earlynerd/ELRS-haptics/hardware/archive/combined-project/README.md

# Archived combined project

This superseded eight-island project was moved here intact on 2026-09-13. It includes the user's top-sheet redraw and the last combined PCB. It is retained for provenance, not active editing.

Open `../../main/main.kicad_pro` and `../../satellite/satellite.kicad_pro` for current work. The end-only R53 bridge is replaced by JP1 on the universal satellite.

Original hashes and an independent snapshot are under `../../backups/before-two-projects/`. No components were missing from the redraw; its two split power aliases are repaired in the new projects.
