earlynerd/ELRS-haptics/hardware/preview/lra-contact.png

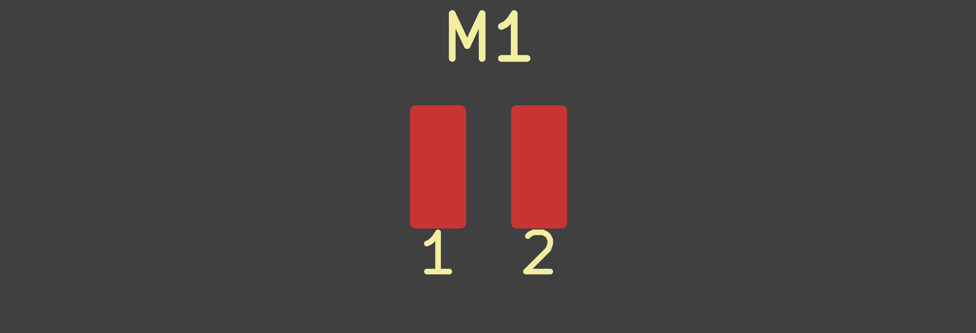
hardware/preview/lra-contact.png
