earlynerd/ELRS-haptics/hardware/preview/pack-protection/power.png

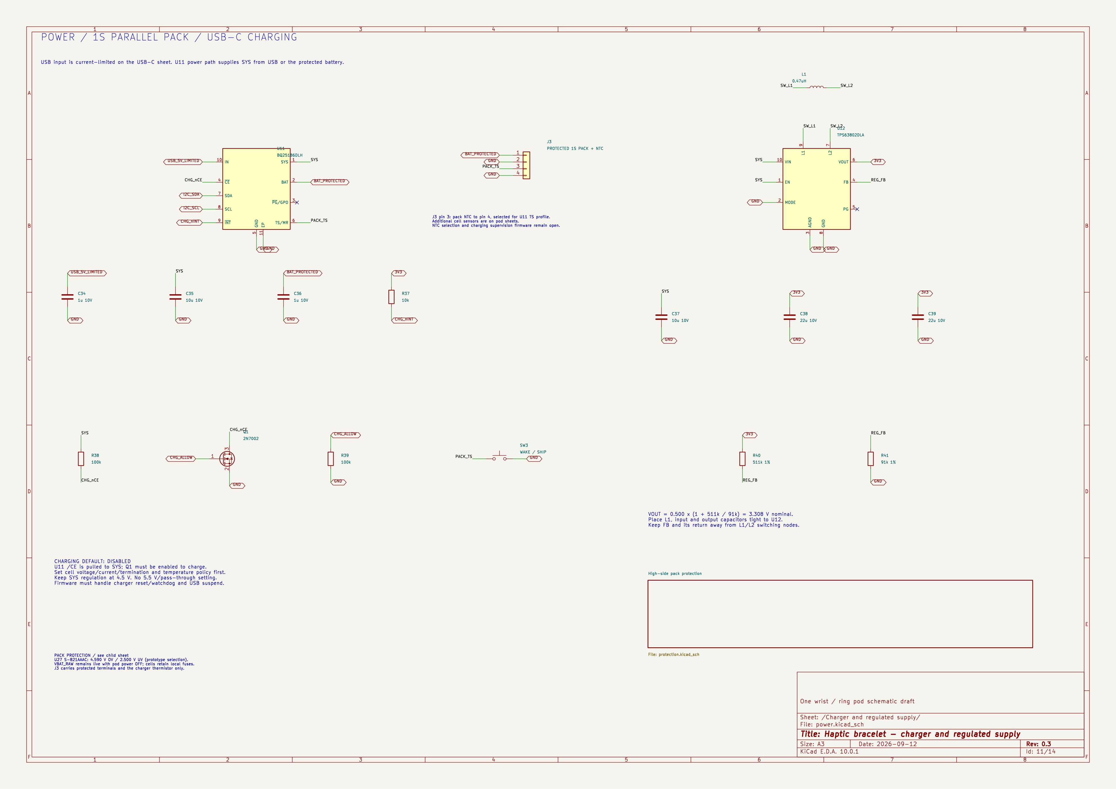
hardware/preview/pack-protection/power.png
