earlynerd/ELRS-haptics/hardware/preview/pack-protection/protection.png

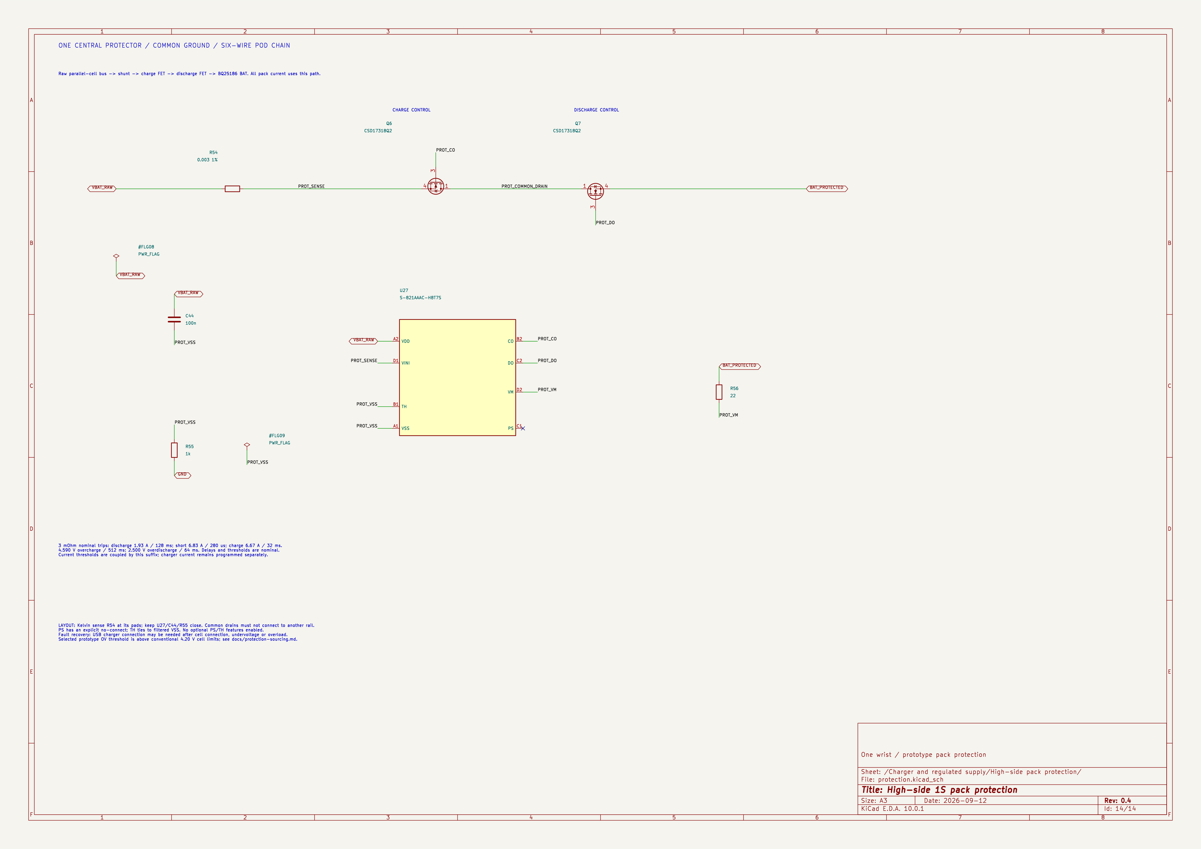
hardware/preview/pack-protection/protection.png
