earlynerd/ELRS-haptics/hardware/preview/placement.png

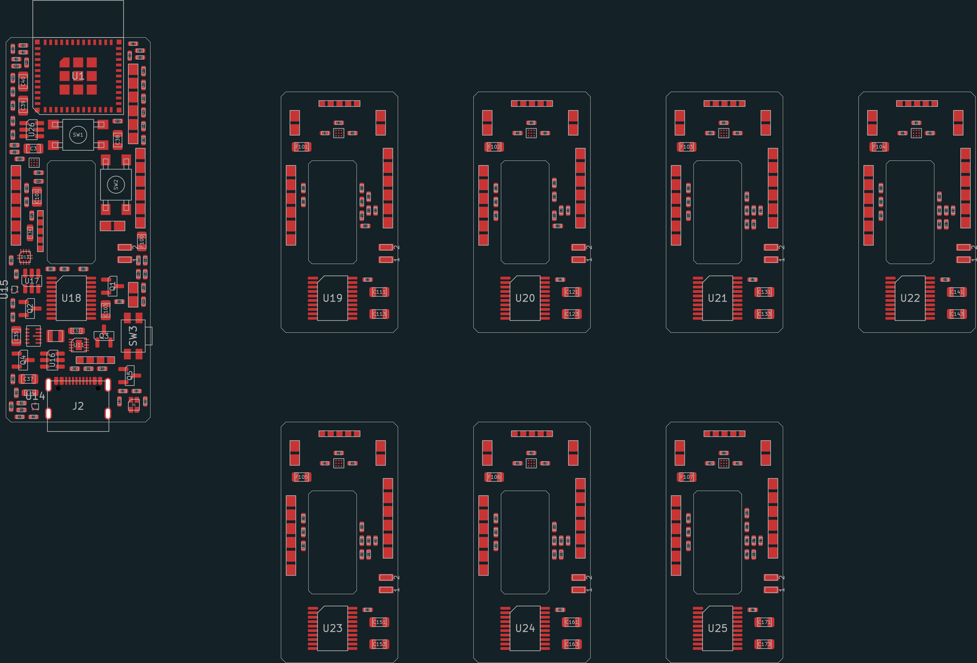
hardware/preview/placement.png
