earlynerd/ELRS-haptics/hardware/preview/protected-cells/haptic-bracelet-Eight ring pods-Pod 0 _ U18.png

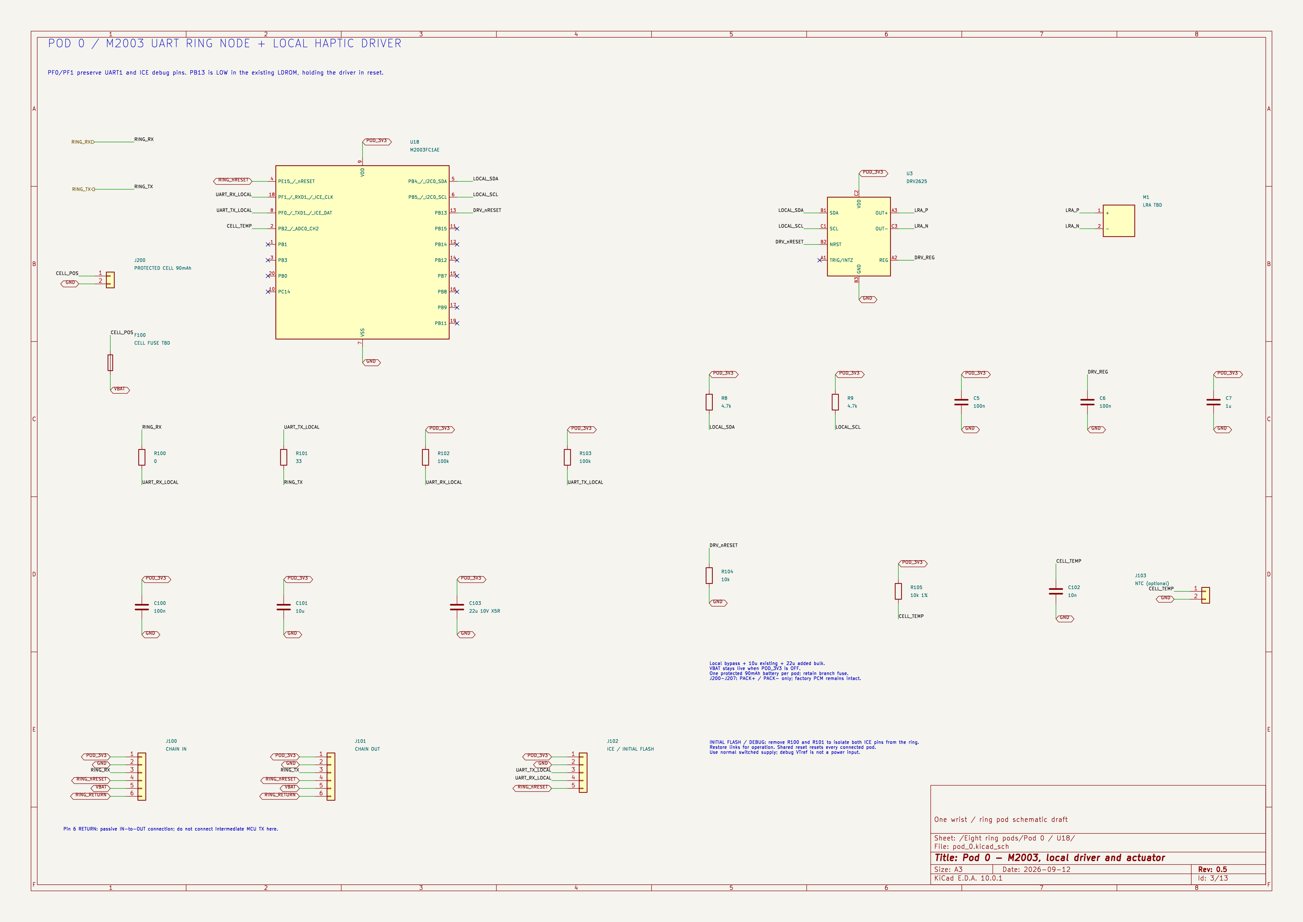
hardware/preview/protected-cells/haptic-bracelet-Eight ring pods-Pod 0 _ U18.png
