earlynerd/ELRS-haptics/hardware/preview/protected-cells/haptic-bracelet-Eight ring pods.png

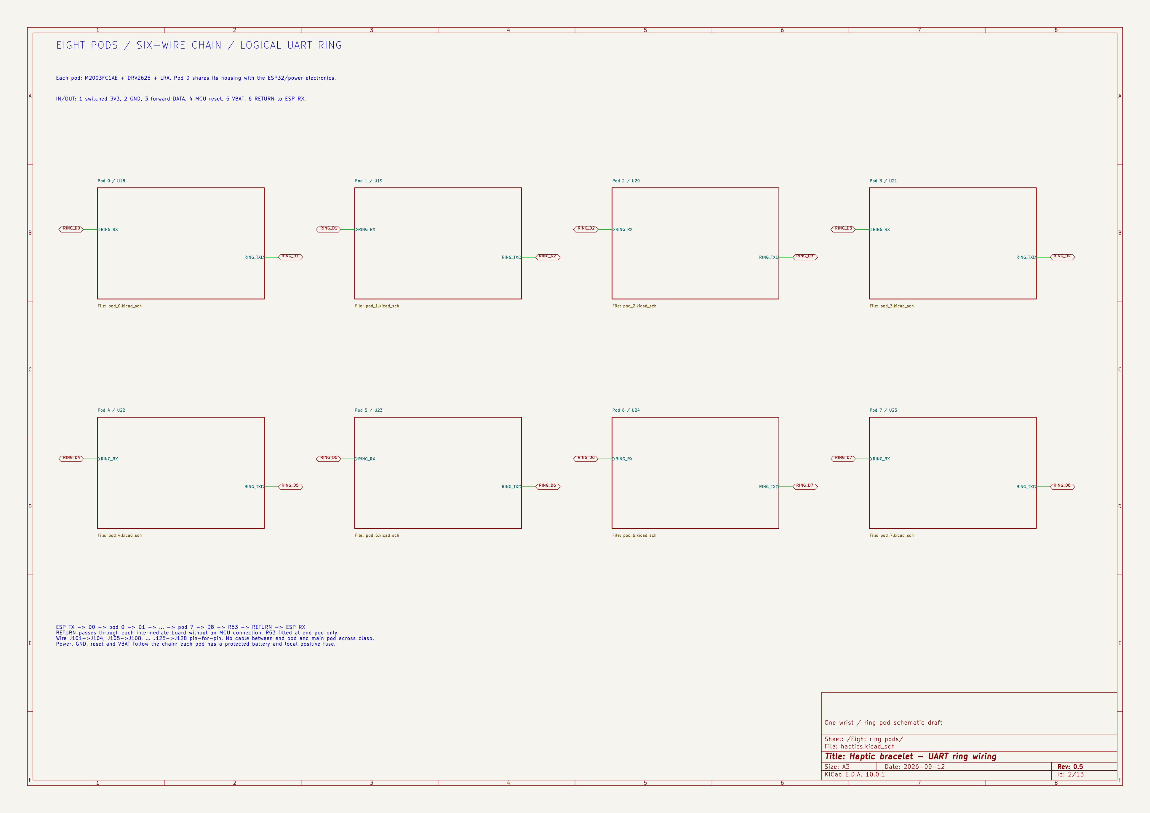
hardware/preview/protected-cells/haptic-bracelet-Eight ring pods.png
