earlynerd/ELRS-haptics/hardware/preview/protected-cells/haptic-bracelet-USB-C data and power.png

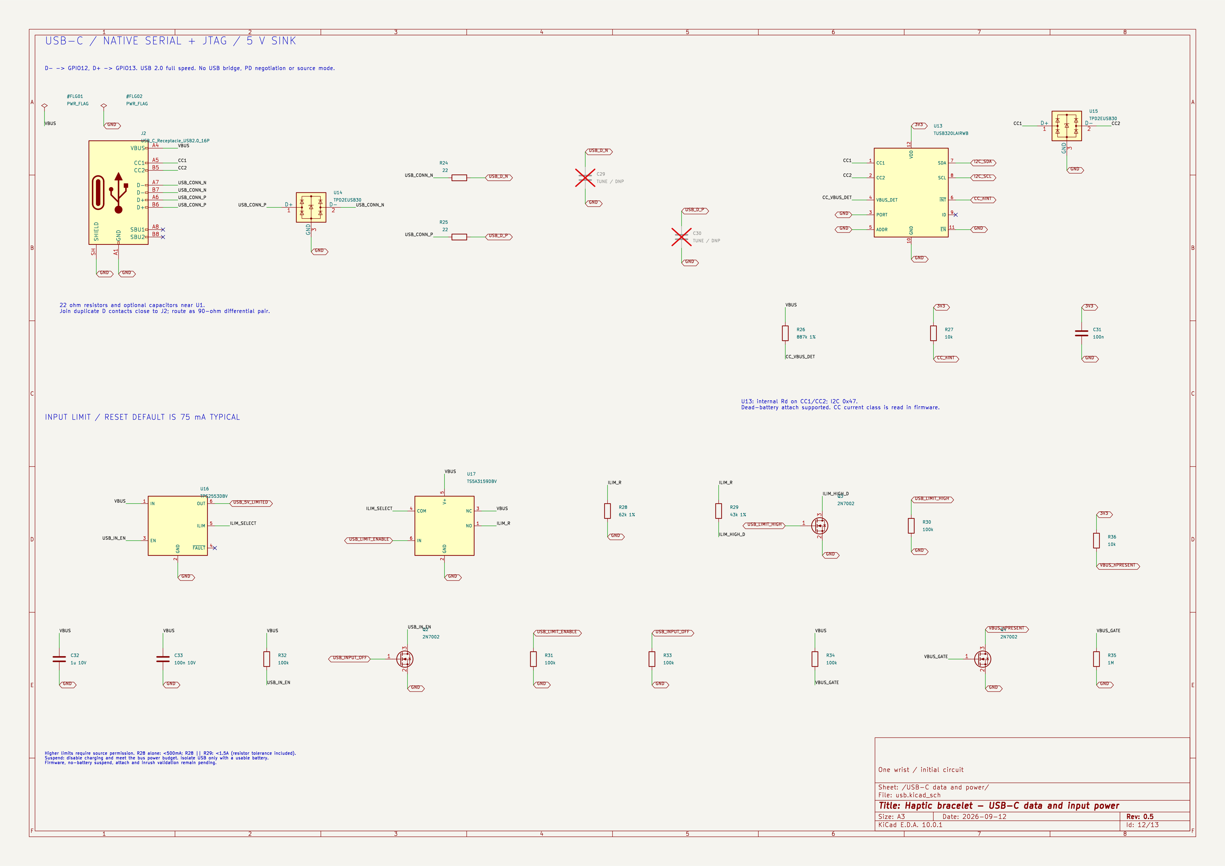
hardware/preview/protected-cells/haptic-bracelet-USB-C data and power.png
