earlynerd/ELRS-haptics/hardware/preview/protected-cells/haptic-bracelet.png

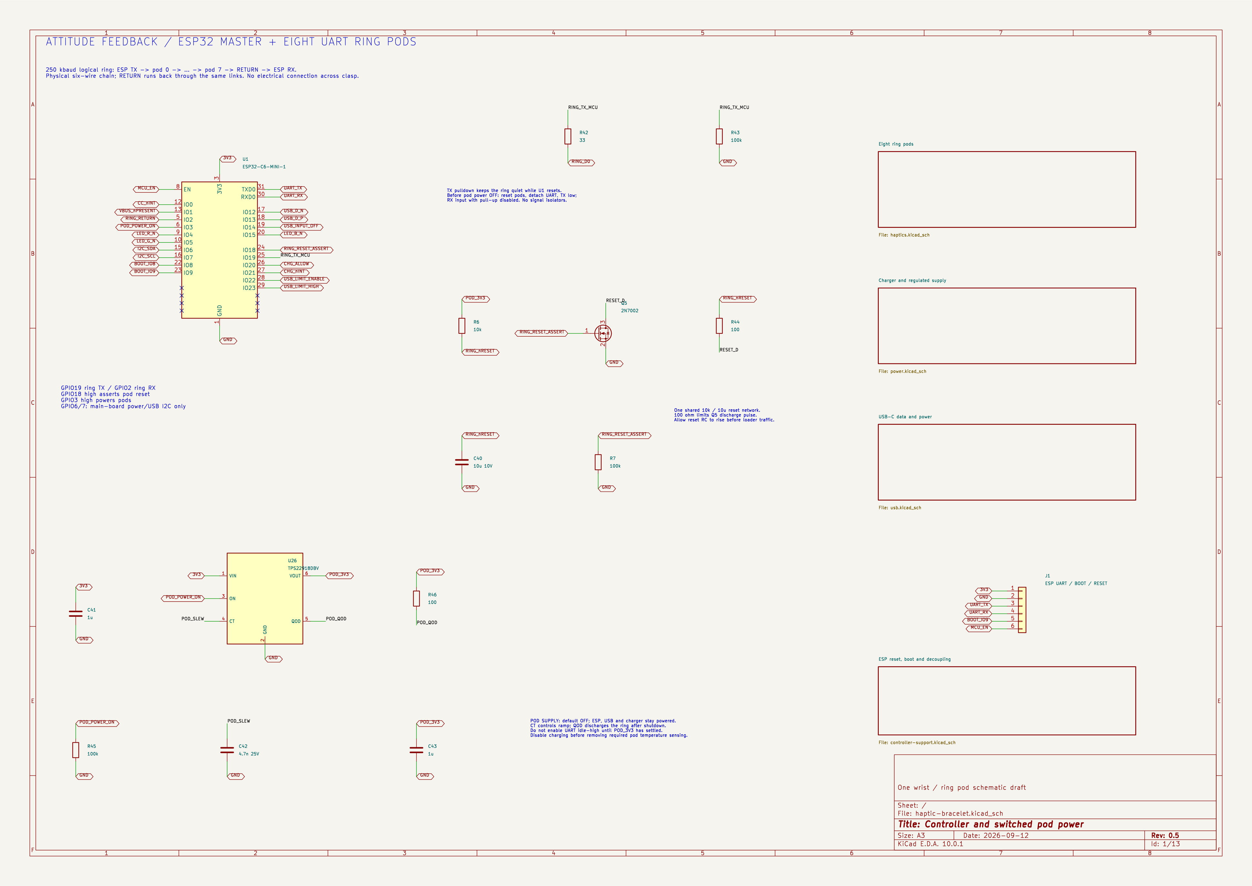
hardware/preview/protected-cells/haptic-bracelet.png
