earlynerd/ELRS-haptics/hardware/preview/ring-revision/haptic-bracelet-ESP reset, boot and decoupling.png

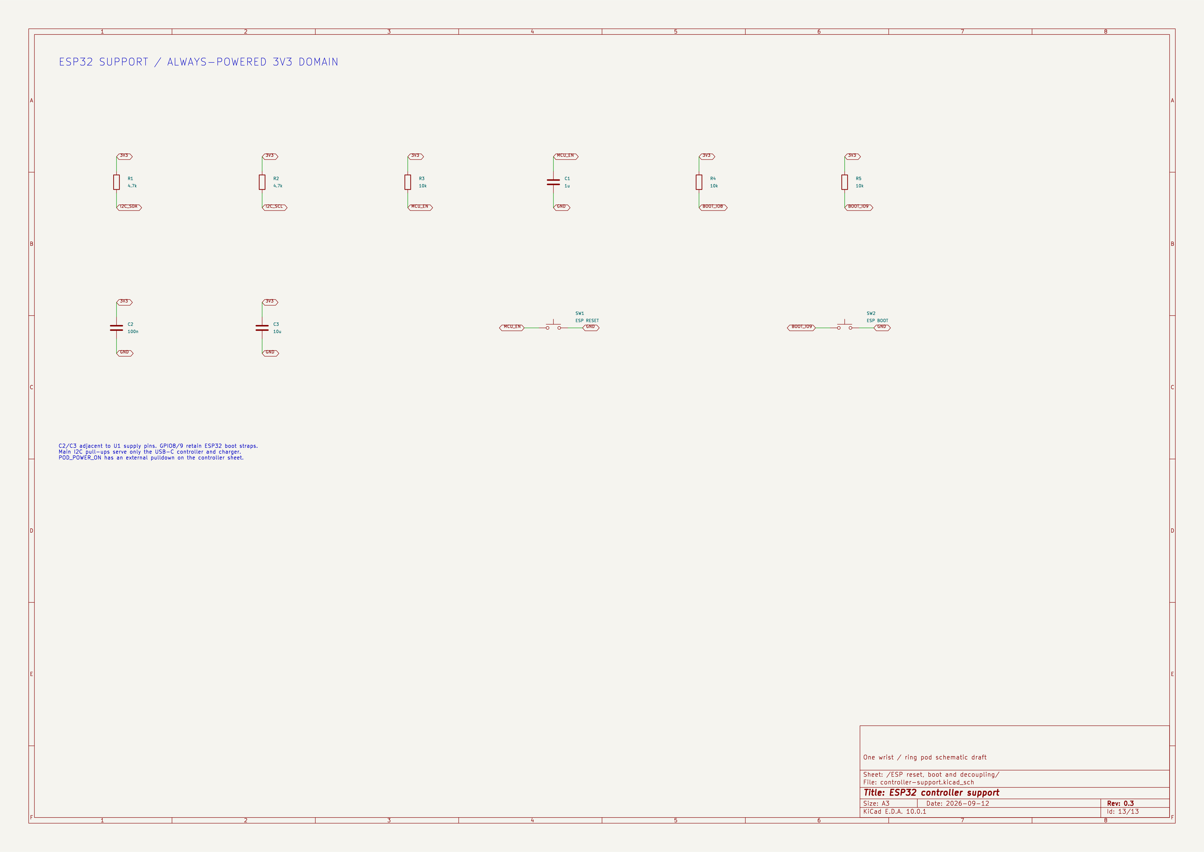
hardware/preview/ring-revision/haptic-bracelet-ESP reset, boot and decoupling.png
