earlynerd/ELRS-haptics/hardware/preview/serial-return/end-pod.png

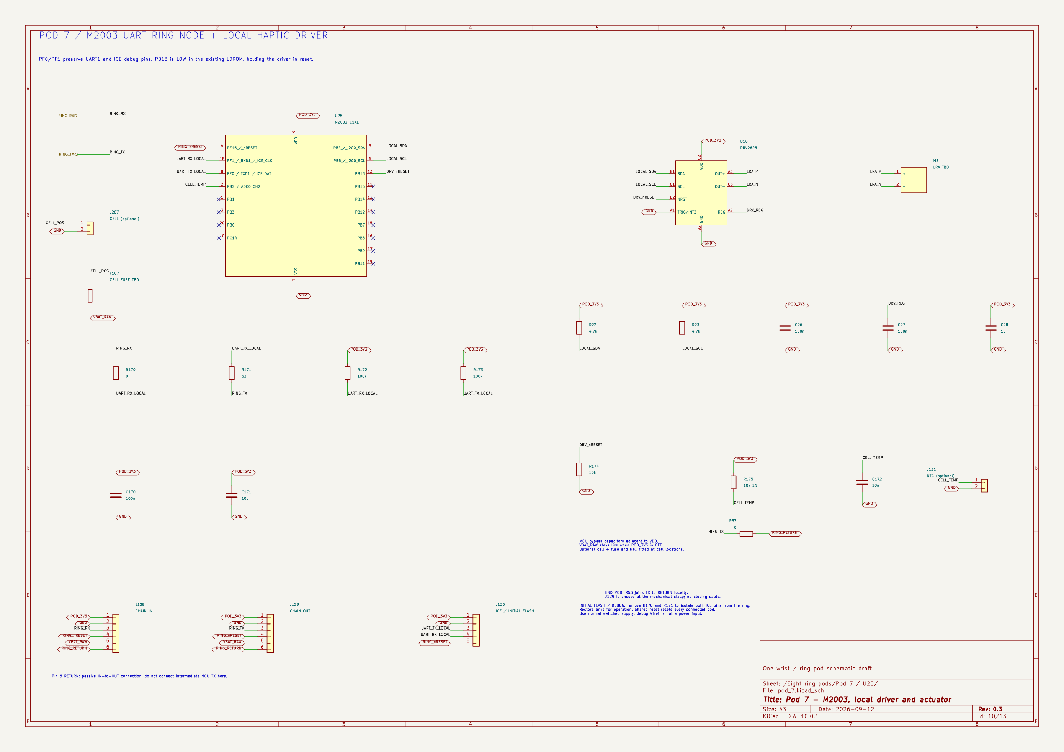
hardware/preview/serial-return/end-pod.png
