earlynerd/ELRS-haptics/hardware/verification/routing-v09/main-placement-proposal.png

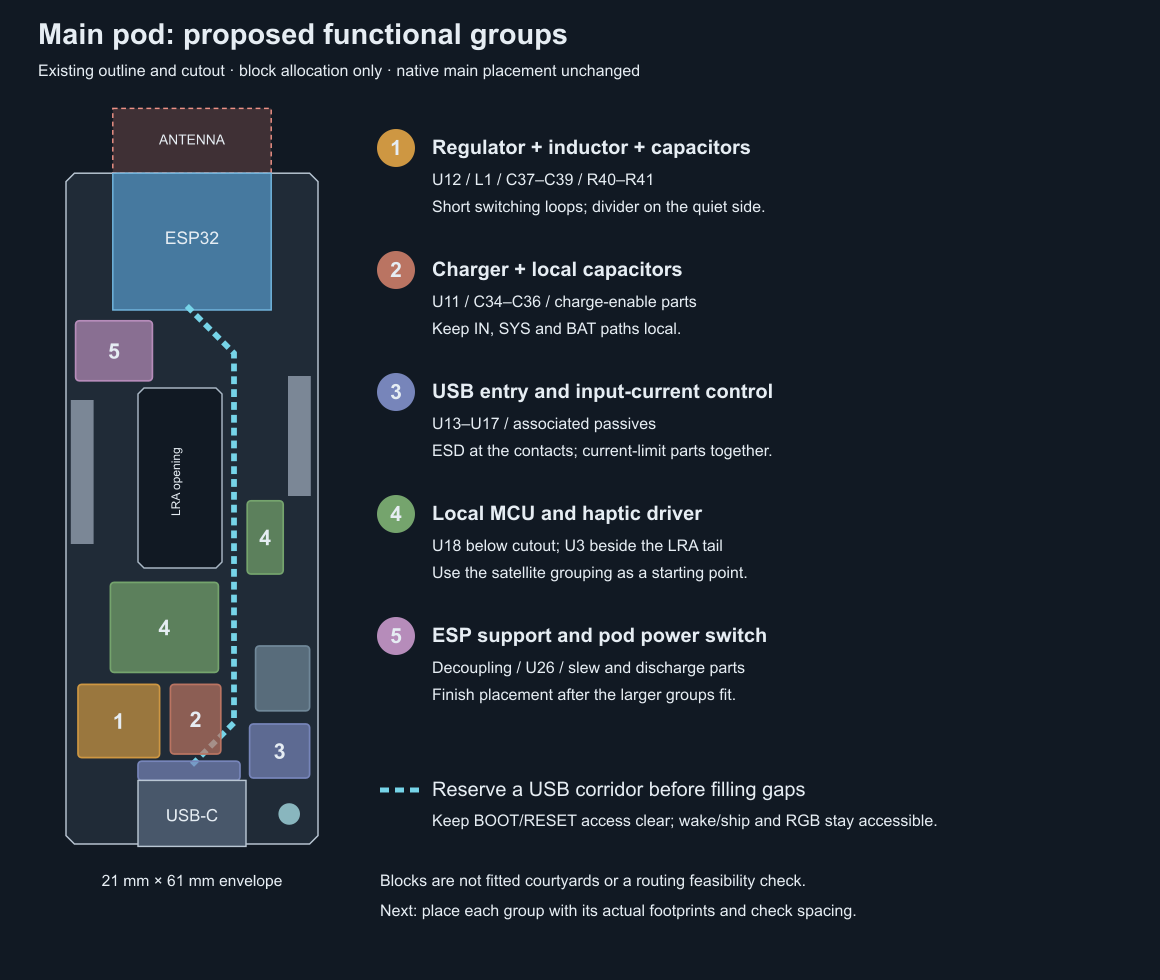
hardware/verification/routing-v09/main-placement-proposal.png
