earlynerd/ELRS-haptics/hardware/verification/routing-v09/overview.png

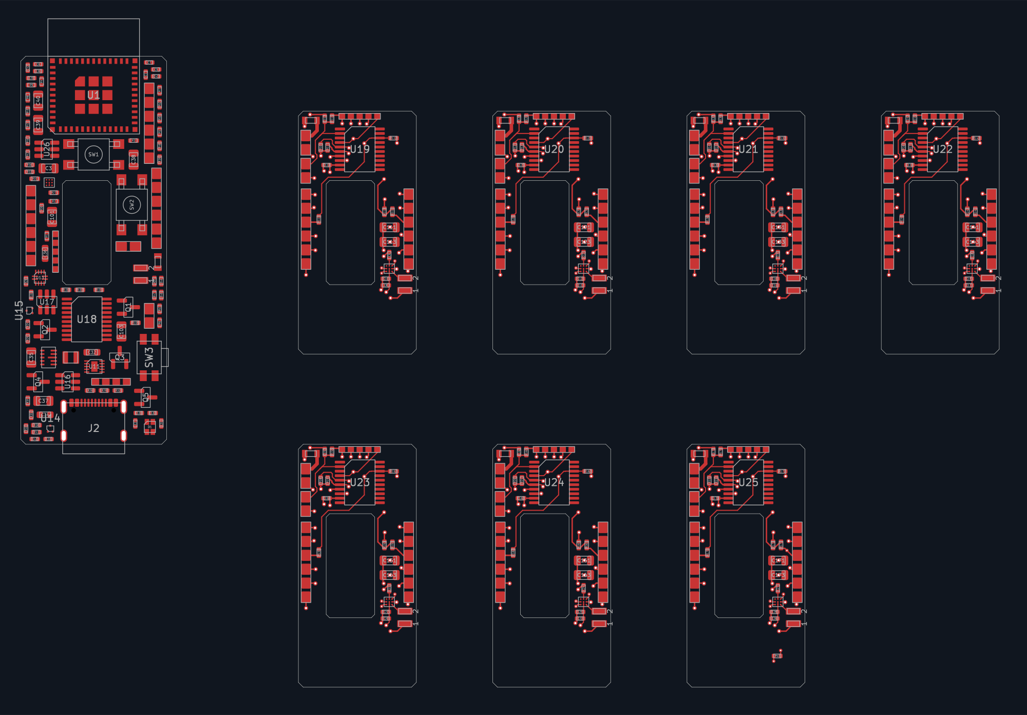
hardware/verification/routing-v09/overview.png
