earlynerd/ELRS-haptics/mechanical/fit-mockup/exploded-preview.png

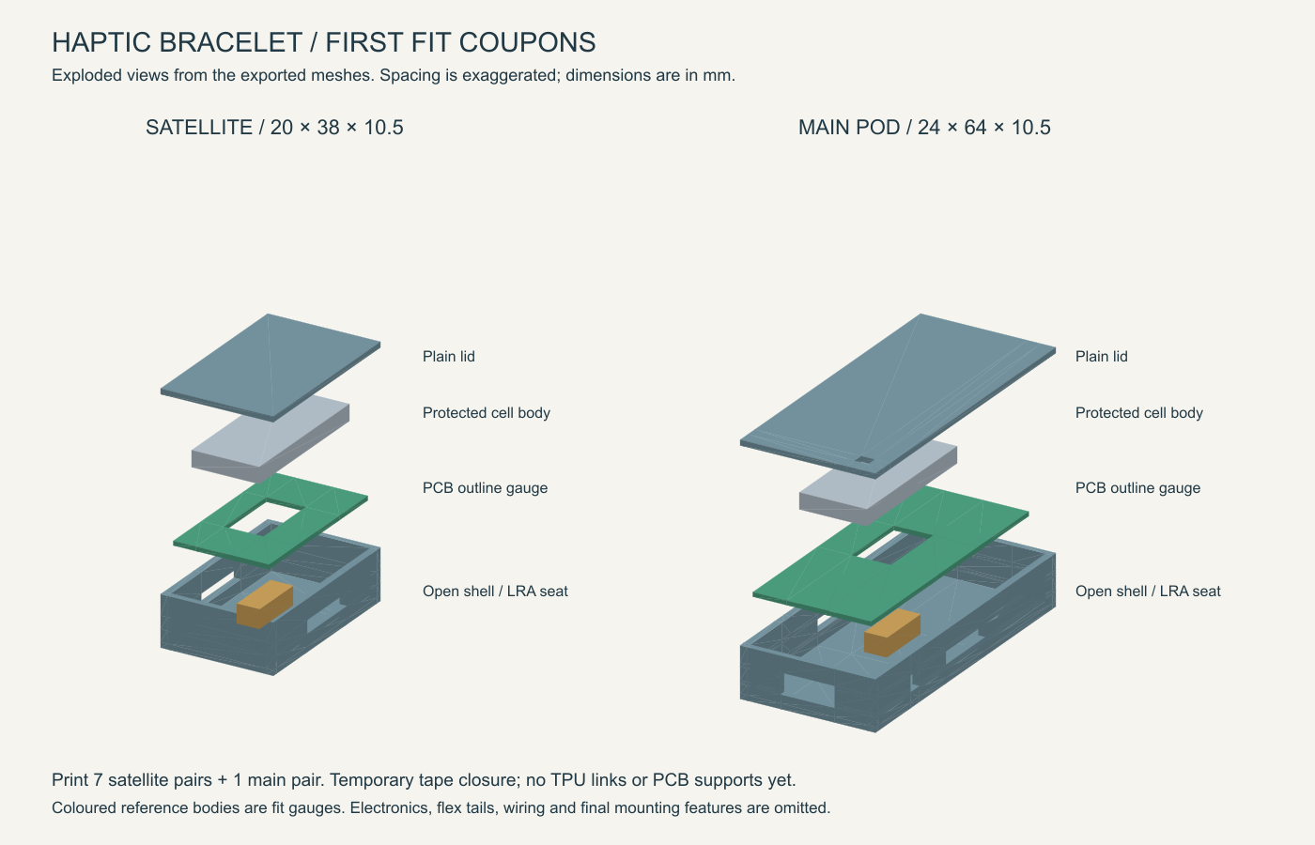
mechanical/fit-mockup/exploded-preview.png
