earlynerd/ELRS-haptics/mechanical/myo-flat-v0.11/design-overview.png

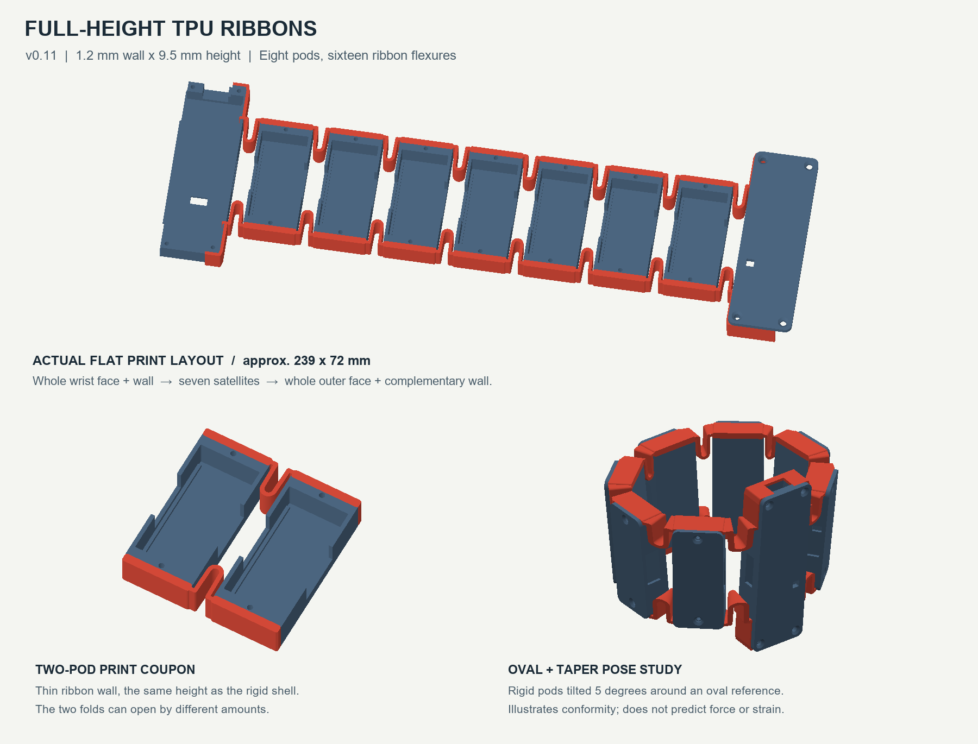
mechanical/myo-flat-v0.11/design-overview.png
