earlynerd/ELRS-haptics/mechanical/myo-flat-v0.11/ribbon-flexure-detail.png

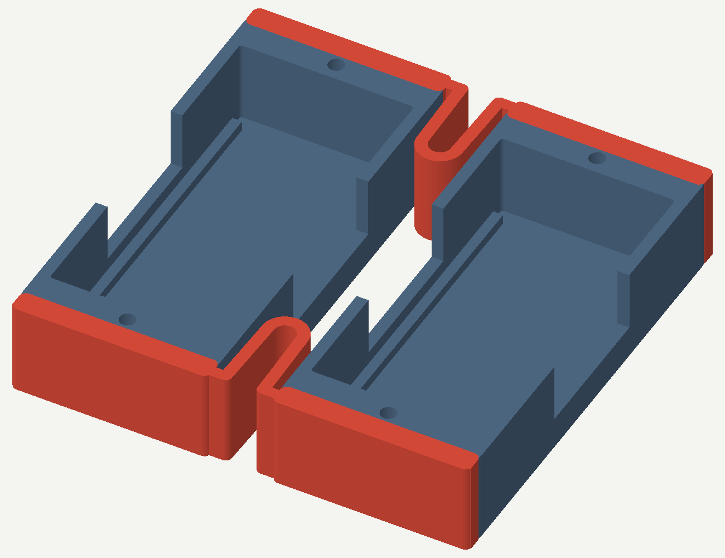
mechanical/myo-flat-v0.11/ribbon-flexure-detail.png
