earlynerd/ELRS-haptics/mechanical/pod-study/pod-dimensions.png

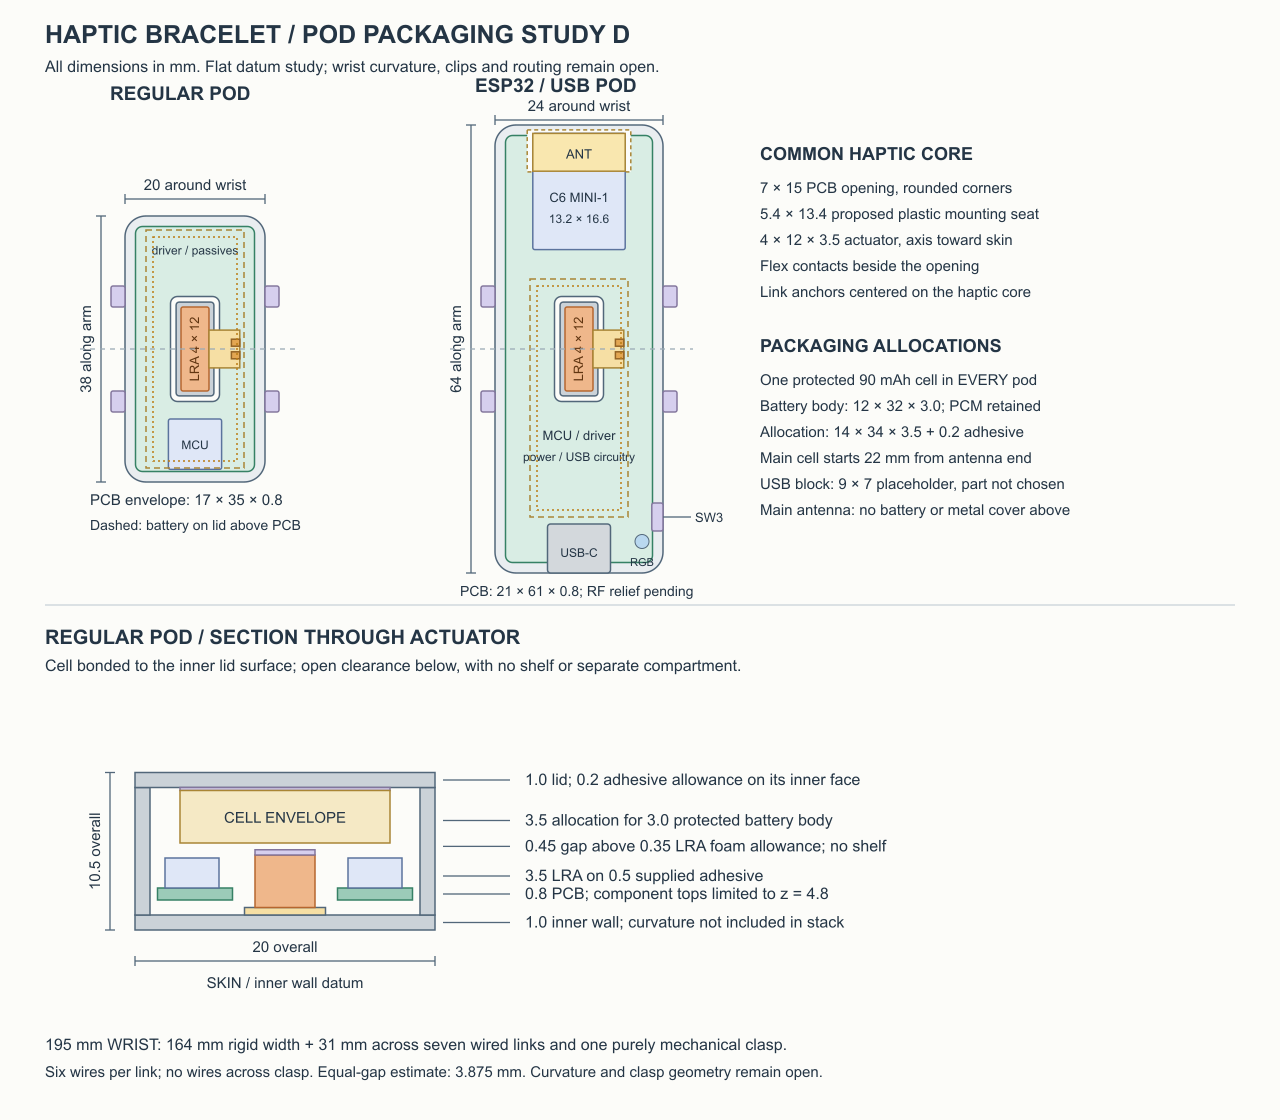
mechanical/pod-study/pod-dimensions.png
