earlynerd/ELRS-haptics/mechanical/fit-mockup/print/satellite-lid.stl

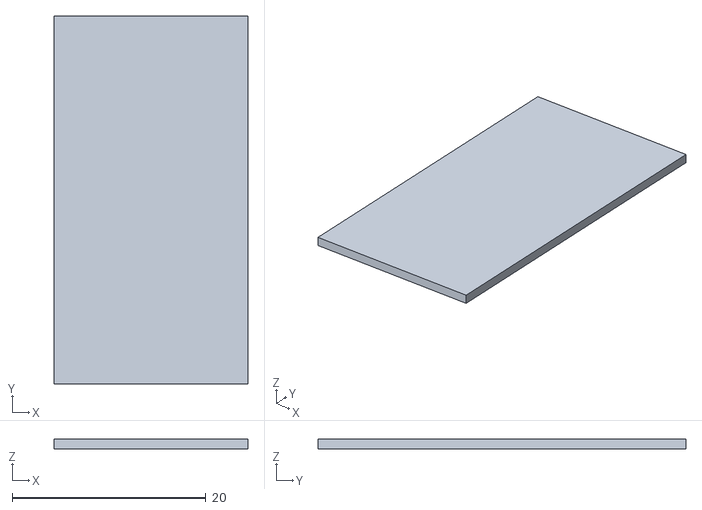
[picture p36: CAD file, 2026-09-14]
mechanical/fit-mockup/print/satellite-lid.stl
20.0 x 38.0 x 1.00
