earlynerd/ELRS-haptics/mechanical/fit-mockup/reference-only/satellite-pcb-gauge.stl

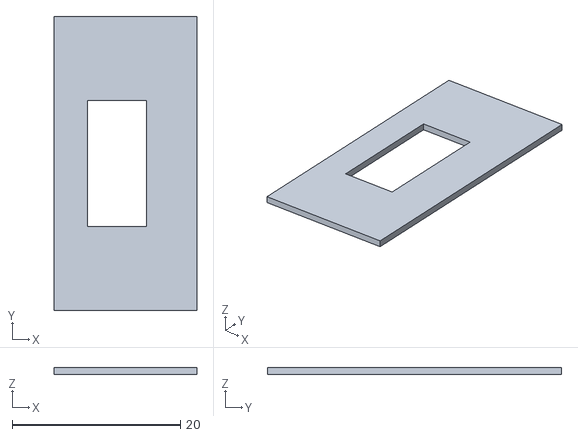
[picture p37: CAD file, 2026-09-14]
mechanical/fit-mockup/reference-only/satellite-pcb-gauge.stl
17.0 x 35.0 x 0.8
