earlynerd/ELRS-haptics/mechanical/myo-flat-v0.11/print/coupon-rigid.stl

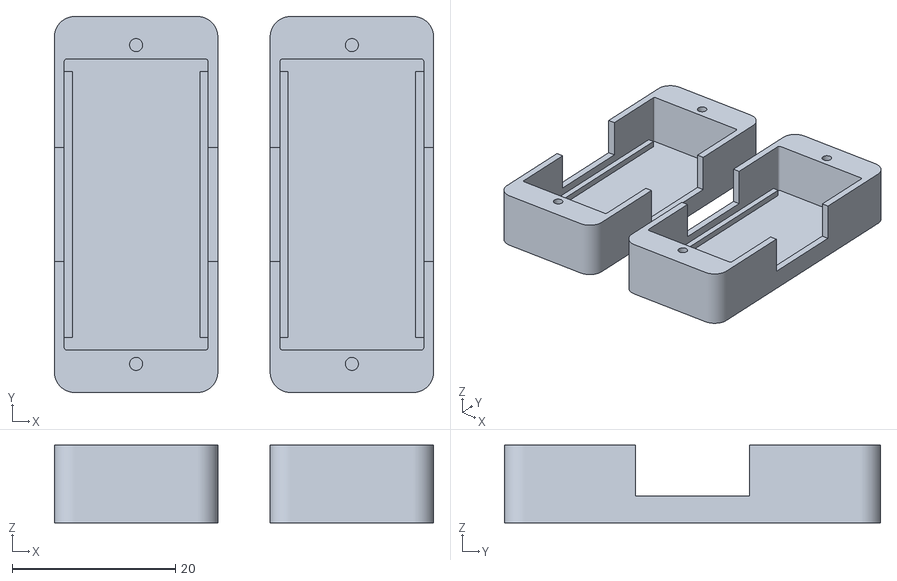
[picture p38: CAD file, 2026-09-17]
mechanical/myo-flat-v0.11/print/coupon-rigid.stl
46.4 x 46.0 x 9.50
