earlynerd/ELRS-haptics/mechanical/myo-flat-v0.11/print/coupon-tpu.stl

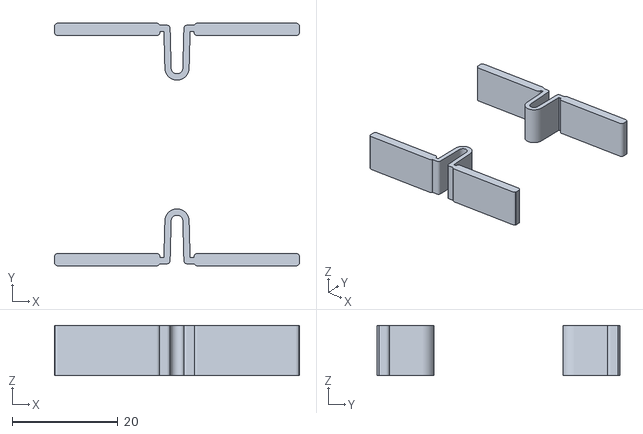
[picture p39: CAD file, 2026-09-17]
mechanical/myo-flat-v0.11/print/coupon-tpu.stl
46.4 x 46.0 x 9.50
