earlynerd/ELRS-haptics/mechanical/myo-flat-v0.11/print/rigid-strip.stl

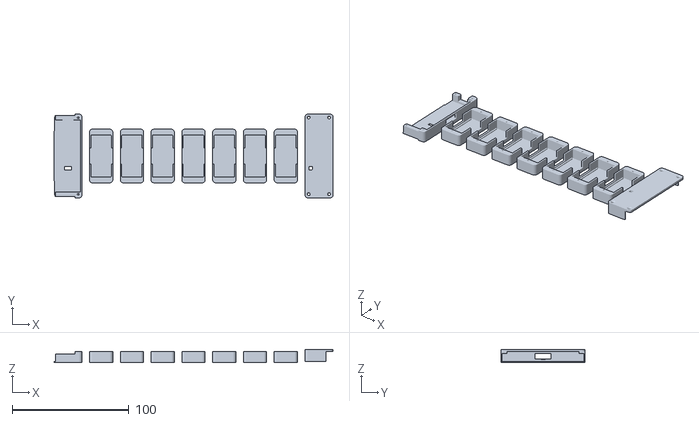
[picture p40: CAD file, 2026-09-17]
mechanical/myo-flat-v0.11/print/rigid-strip.stl
239.2 x 72.0 x 11.5
