earlynerd/ELRS-haptics/mechanical/myo-flat-v0.11/print/closure-coupon-tpu.stl

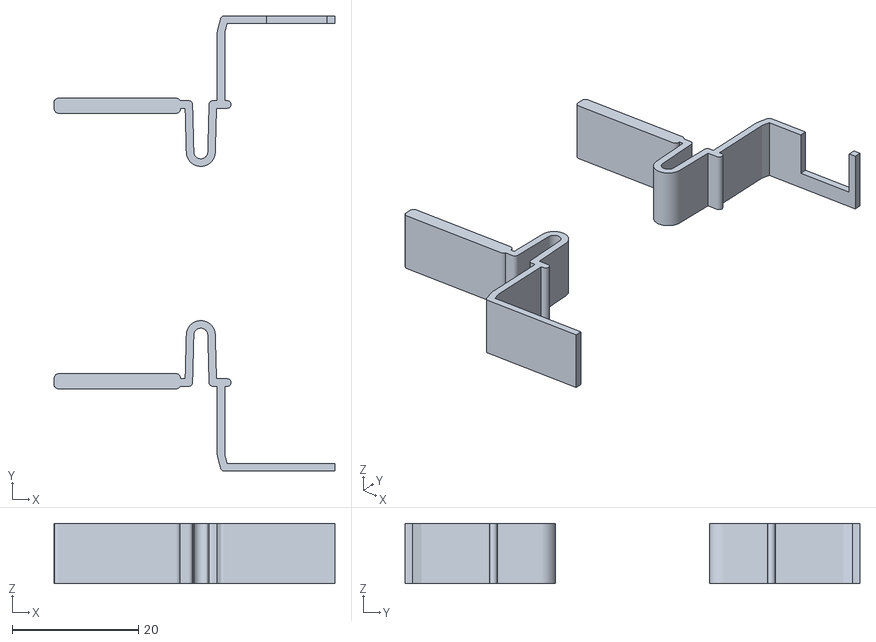
[picture p41: CAD file, 2026-09-17]
mechanical/myo-flat-v0.11/print/closure-coupon-tpu.stl
44.4 x 72.0 x 9.50
