earlynerd/ELRS-haptics/mechanical/myo-flat-v0.11/print/closure-transition-coupon.3mf

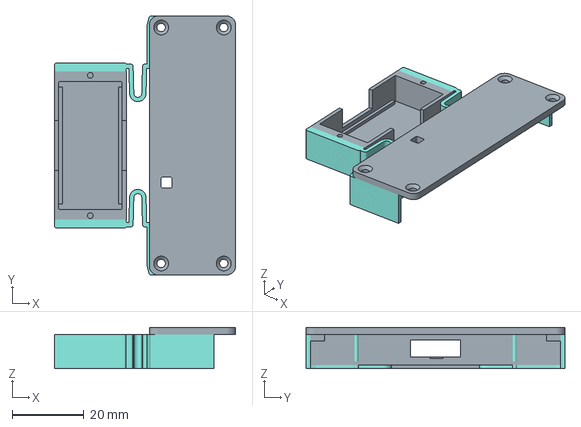
[picture p42: CAD file, 2026-09-17]
mechanical/myo-flat-v0.11/print/closure-transition-coupon.3mf
50.4 x 72.0 x 11.5 mm
