earlynerd/ELRS-haptics/mechanical/myo-flat-v0.11/print/tpu-end-flexures.stl

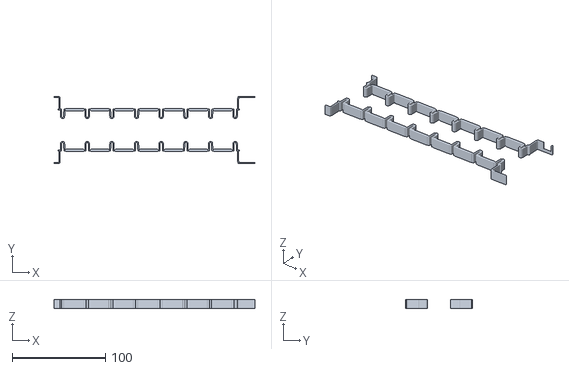
[picture p43: CAD file, 2026-09-17]
mechanical/myo-flat-v0.11/print/tpu-end-flexures.stl
215.2 x 72.0 x 9.50
