earlynerd/ELRS-haptics/mechanical/myo-flat-v0.11/print/satellite-lid.stl

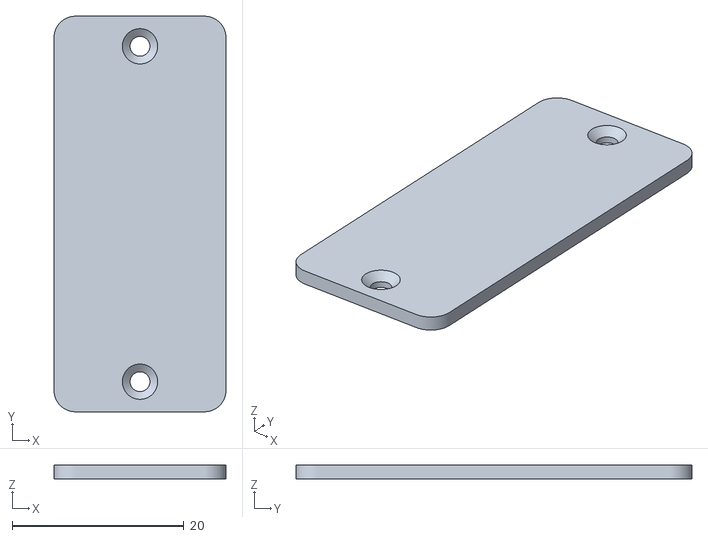
[picture p44: CAD file, 2026-09-17]
mechanical/myo-flat-v0.11/print/satellite-lid.stl
20.0 x 46.0 x 1.60
