earlynerd/ELRS-haptics/hardware/verification/BQ2980-application.png

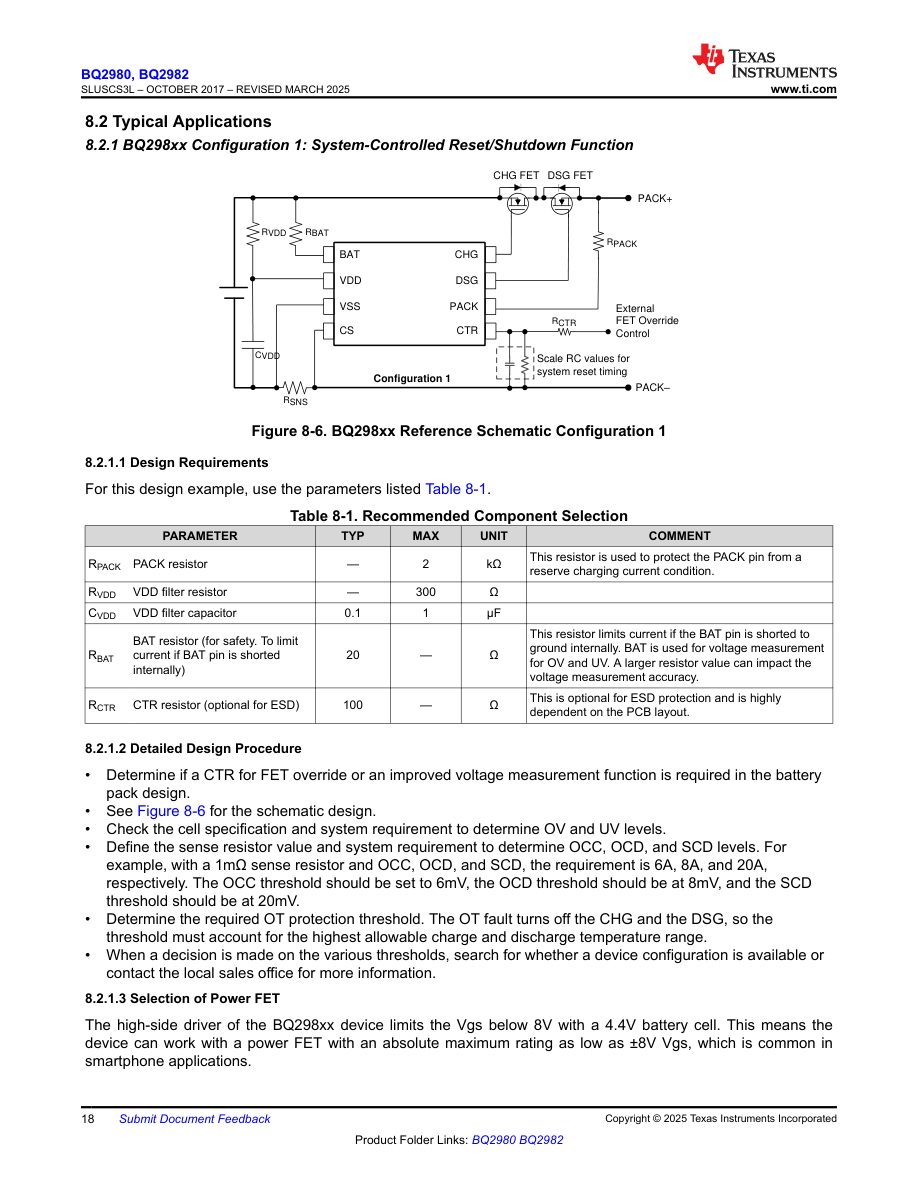
hardware/verification/BQ2980-application.png
