earlynerd/ELRS-haptics/hardware/verification/CSD17318Q2-page-1.png

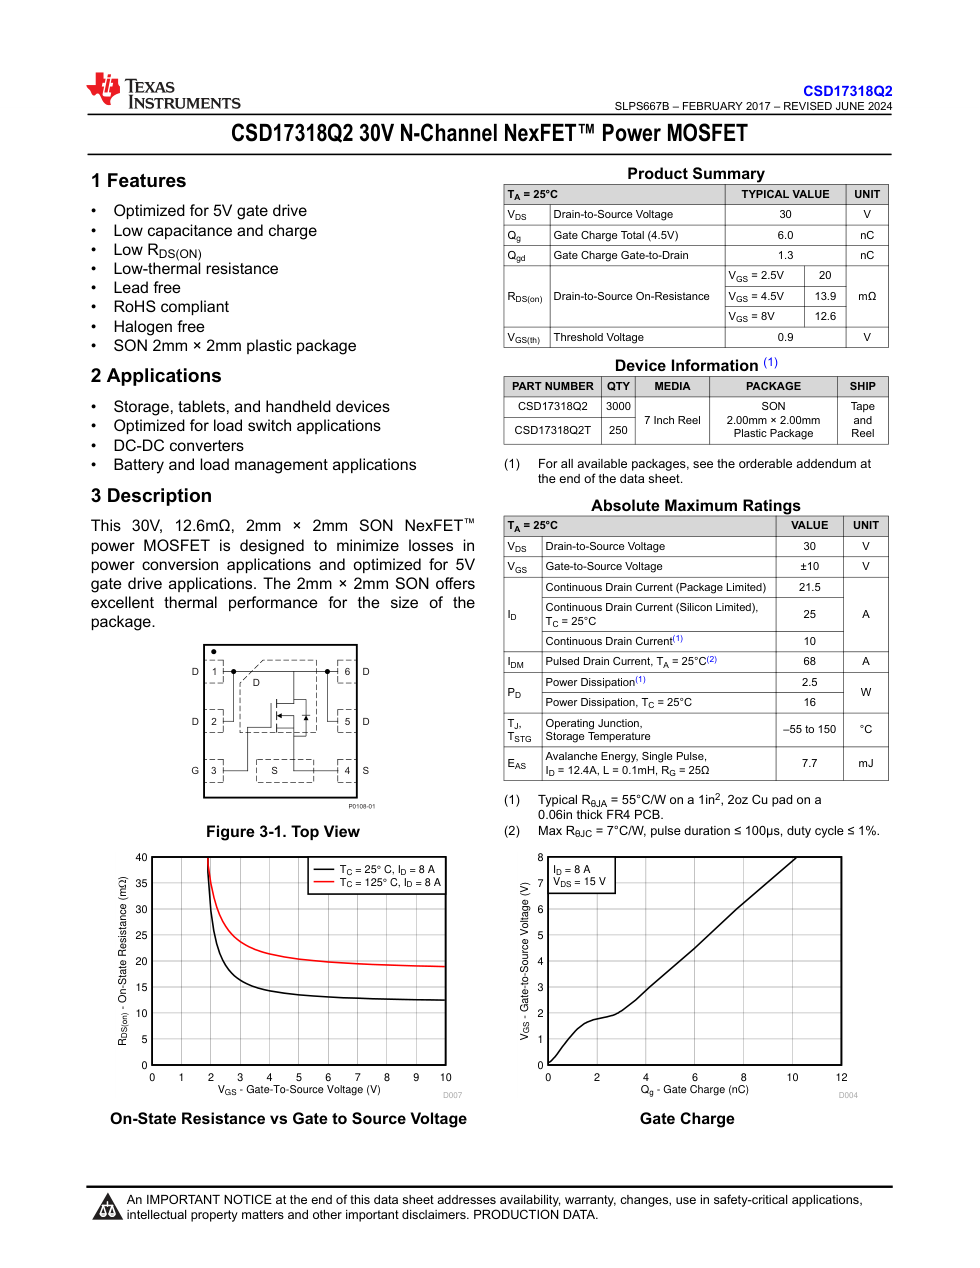
hardware/verification/CSD17318Q2-page-1.png
