earlynerd/ELRS-haptics/hardware/verification/CSD17318Q2-page-10.png

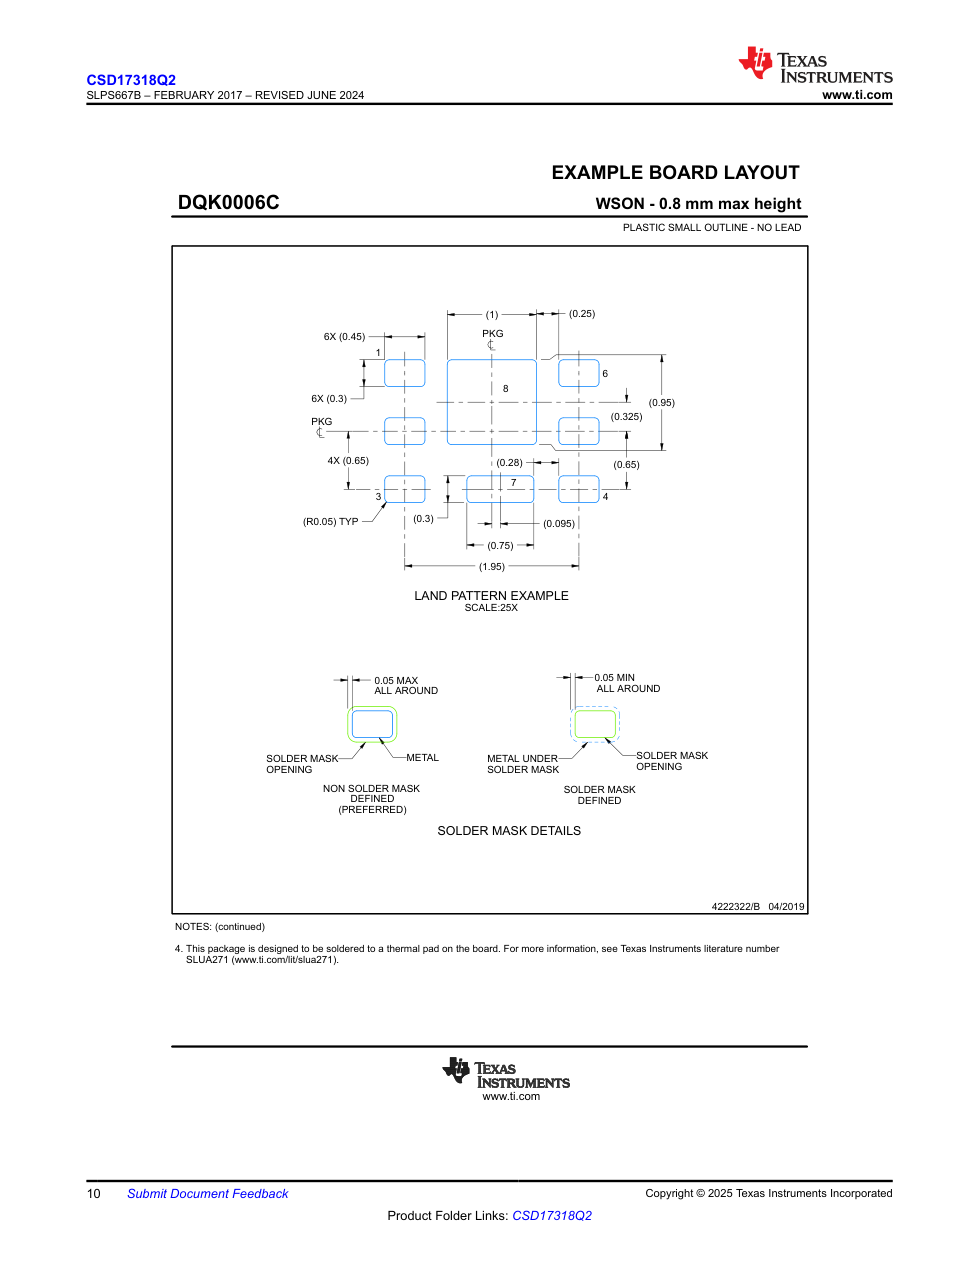
hardware/verification/CSD17318Q2-page-10.png
