earlynerd/ELRS-haptics/hardware/verification/five-pad/local.png

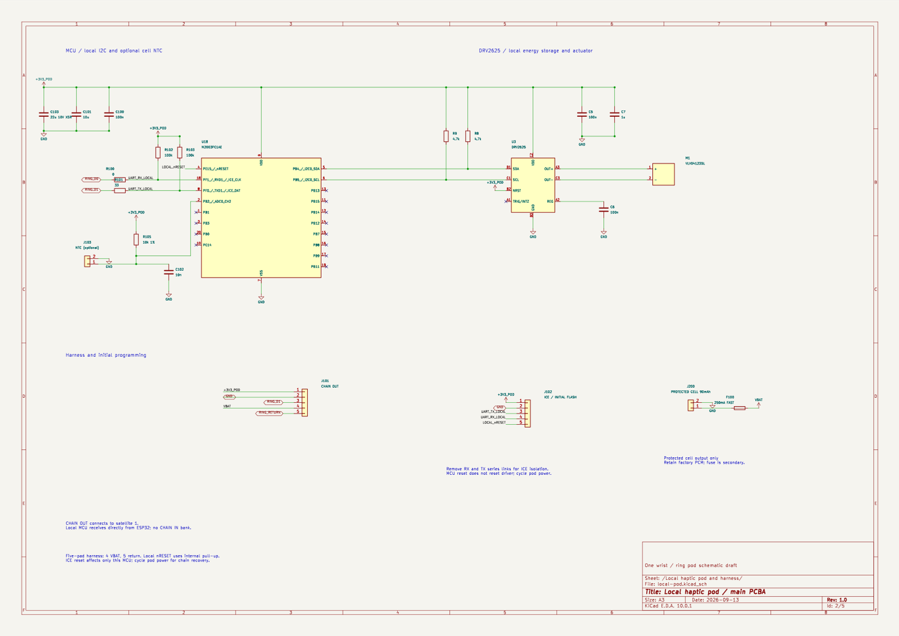
hardware/verification/five-pad/local.png
