earlynerd/ELRS-haptics/hardware/verification/five-wire/main.png

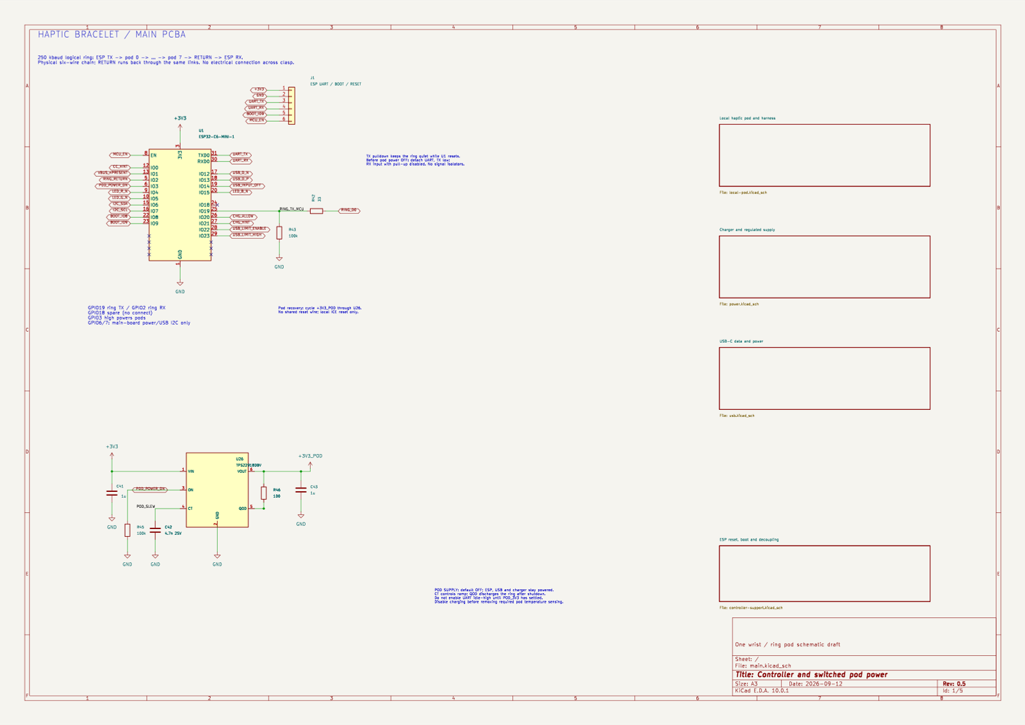
hardware/verification/five-wire/main.png
