earlynerd/ELRS-haptics/hardware/verification/main-placement-v2/placement.png

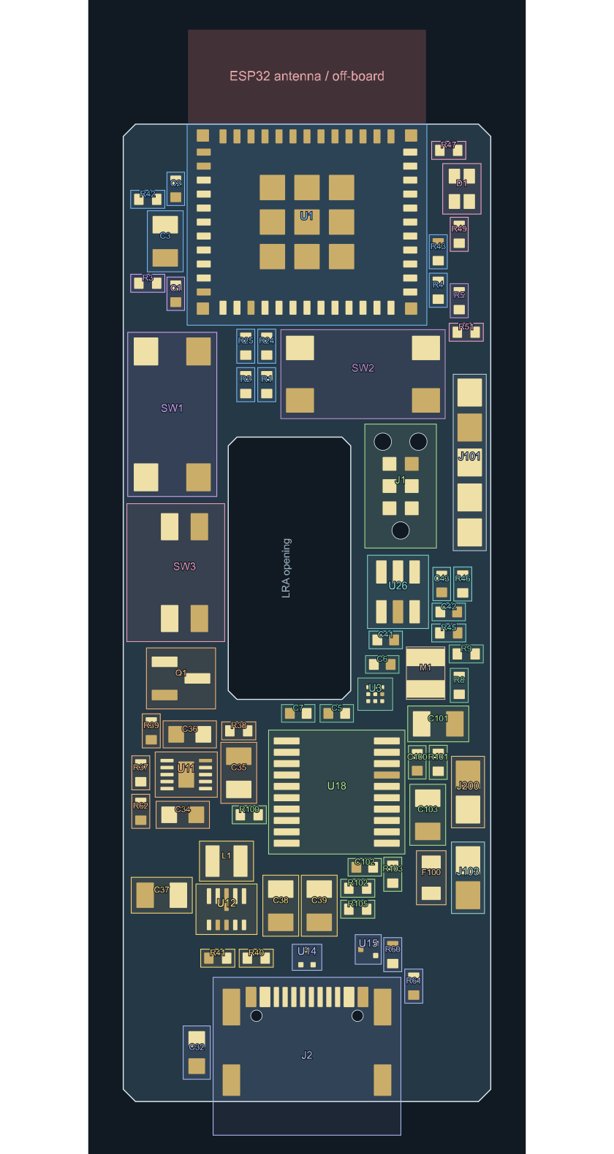
hardware/verification/main-placement-v2/placement.png
