earlynerd/ELRS-haptics/hardware/verification/placement-reference/BQ2518654.png

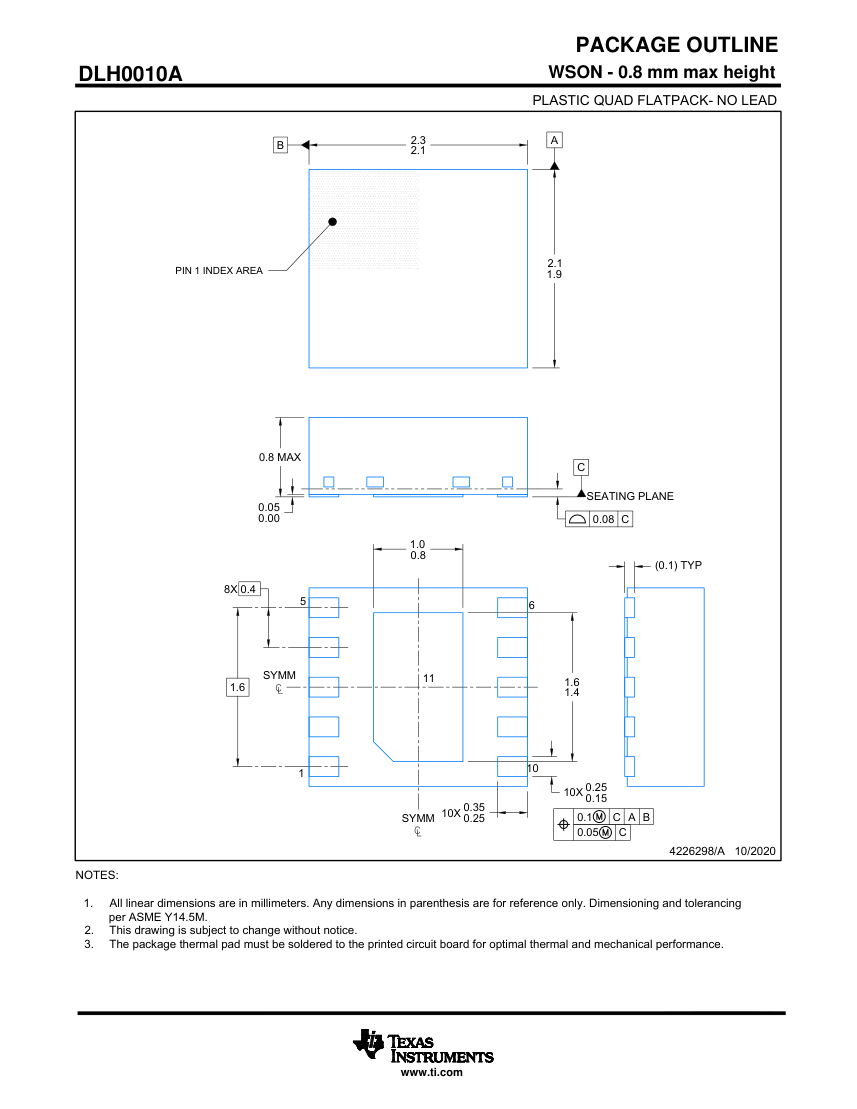
hardware/verification/placement-reference/BQ2518654.png
