earlynerd/ELRS-haptics/hardware/verification/placement-reference/BQ2518655.png

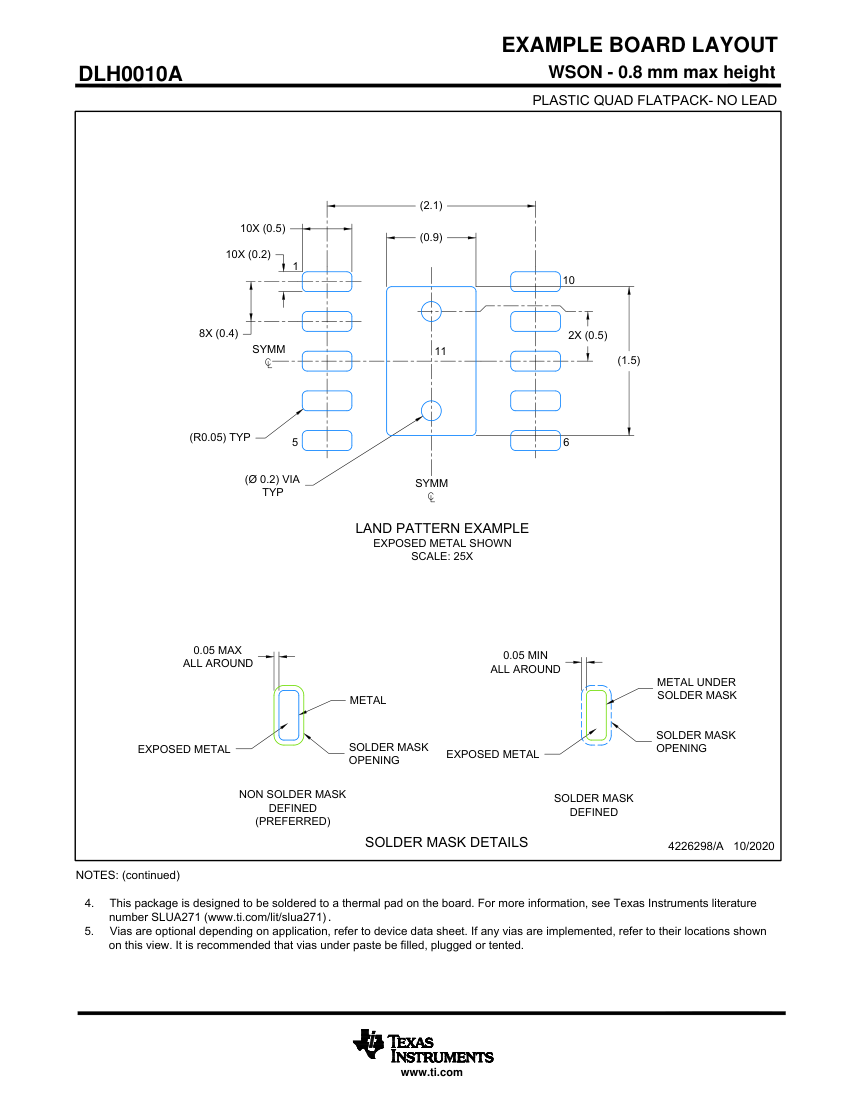
hardware/verification/placement-reference/BQ2518655.png
