earlynerd/ELRS-haptics/hardware/verification/placement-reference/DRV262572.png

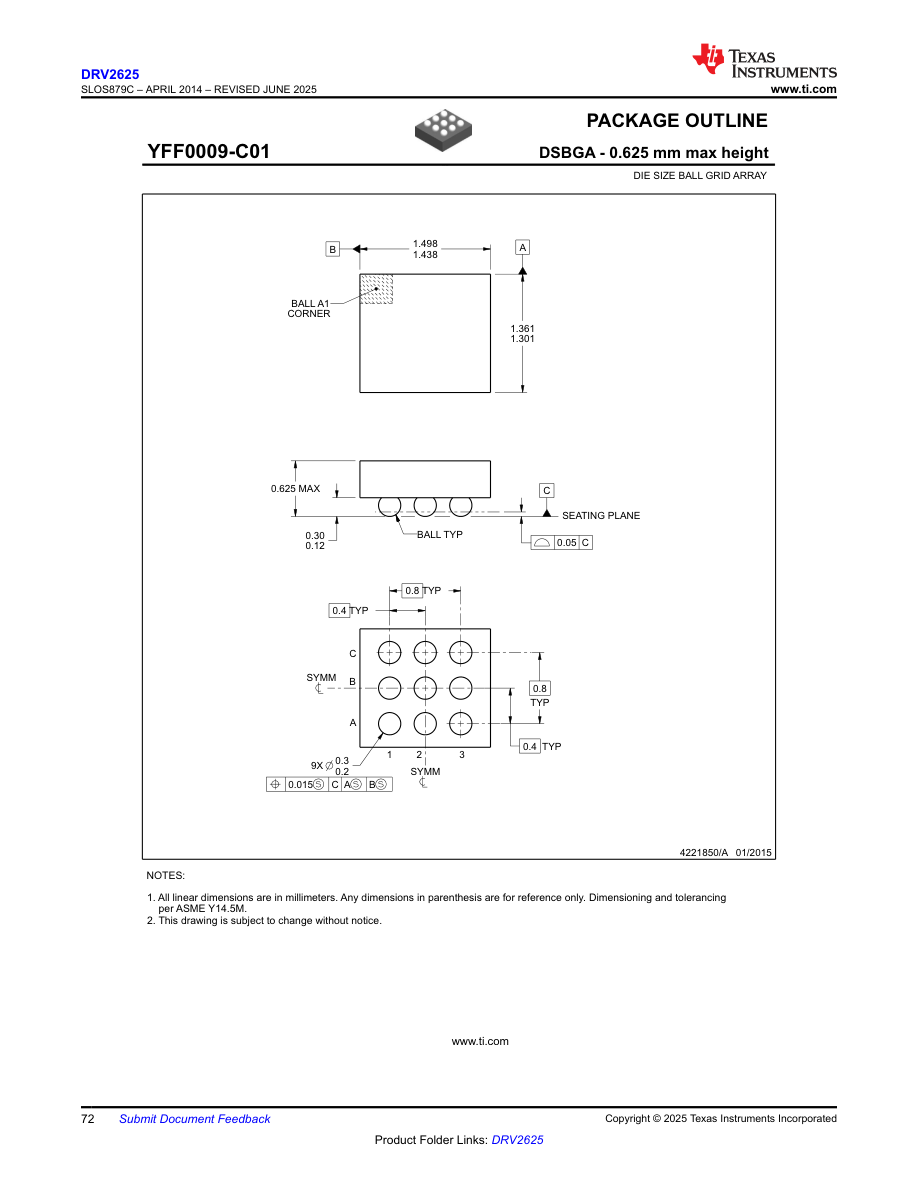
hardware/verification/placement-reference/DRV262572.png
