earlynerd/ELRS-haptics/hardware/verification/placement-reference/DRV262573.png

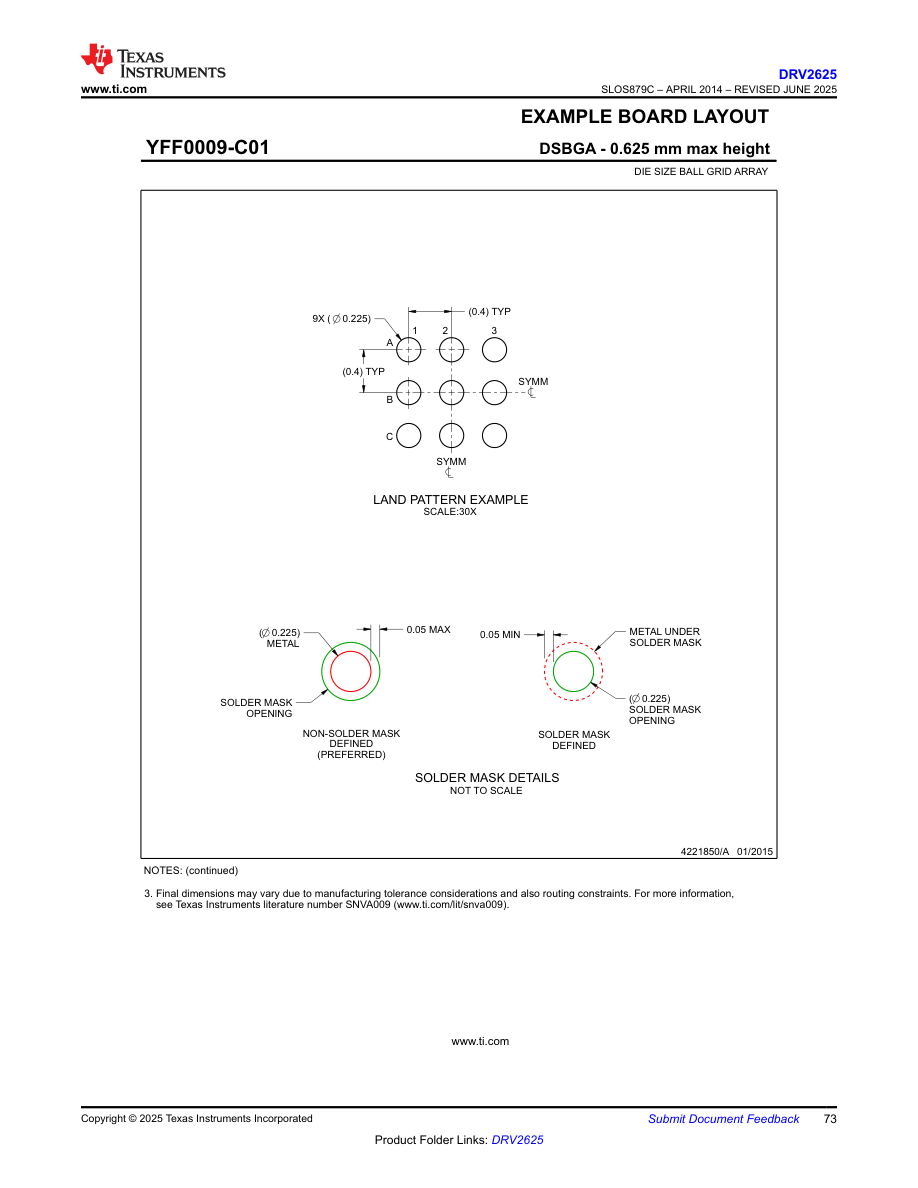
hardware/verification/placement-reference/DRV262573.png
