earlynerd/ELRS-haptics/hardware/verification/placement-reference/DRV262576.png

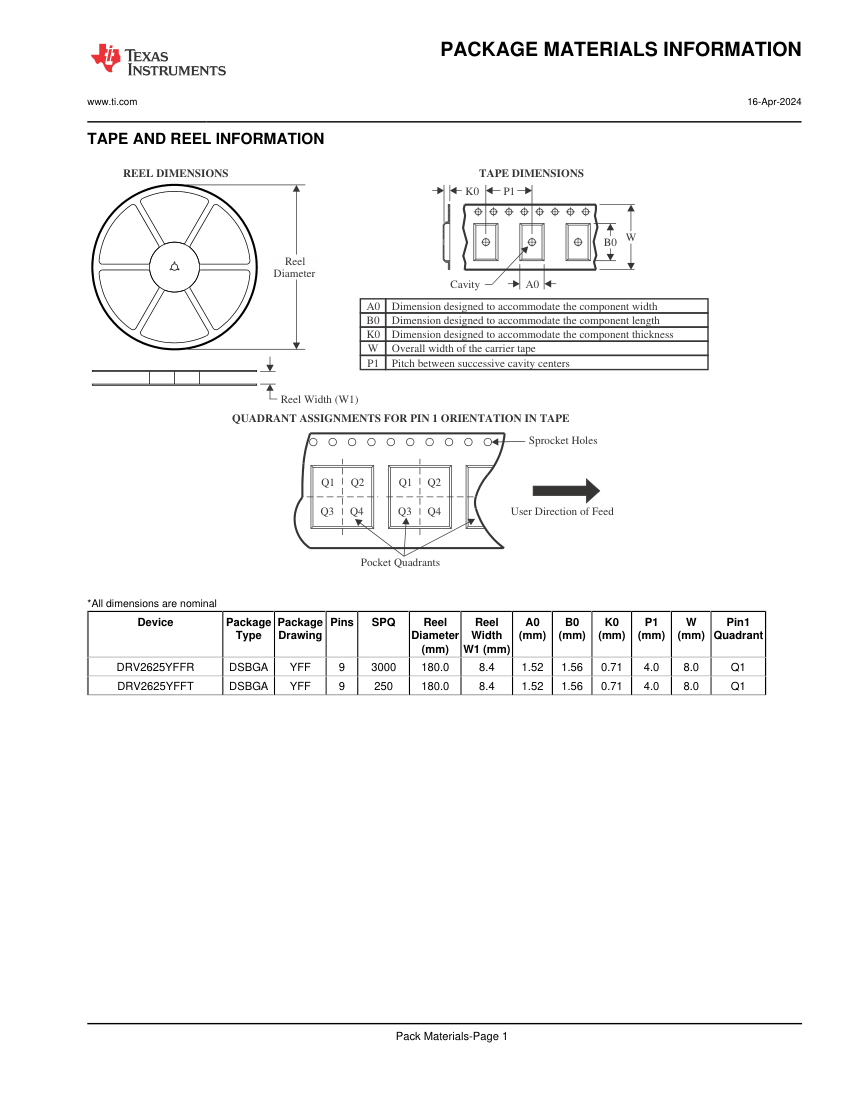
hardware/verification/placement-reference/DRV262576.png
