earlynerd/ELRS-haptics/hardware/verification/placement-reference/DRV262577.png

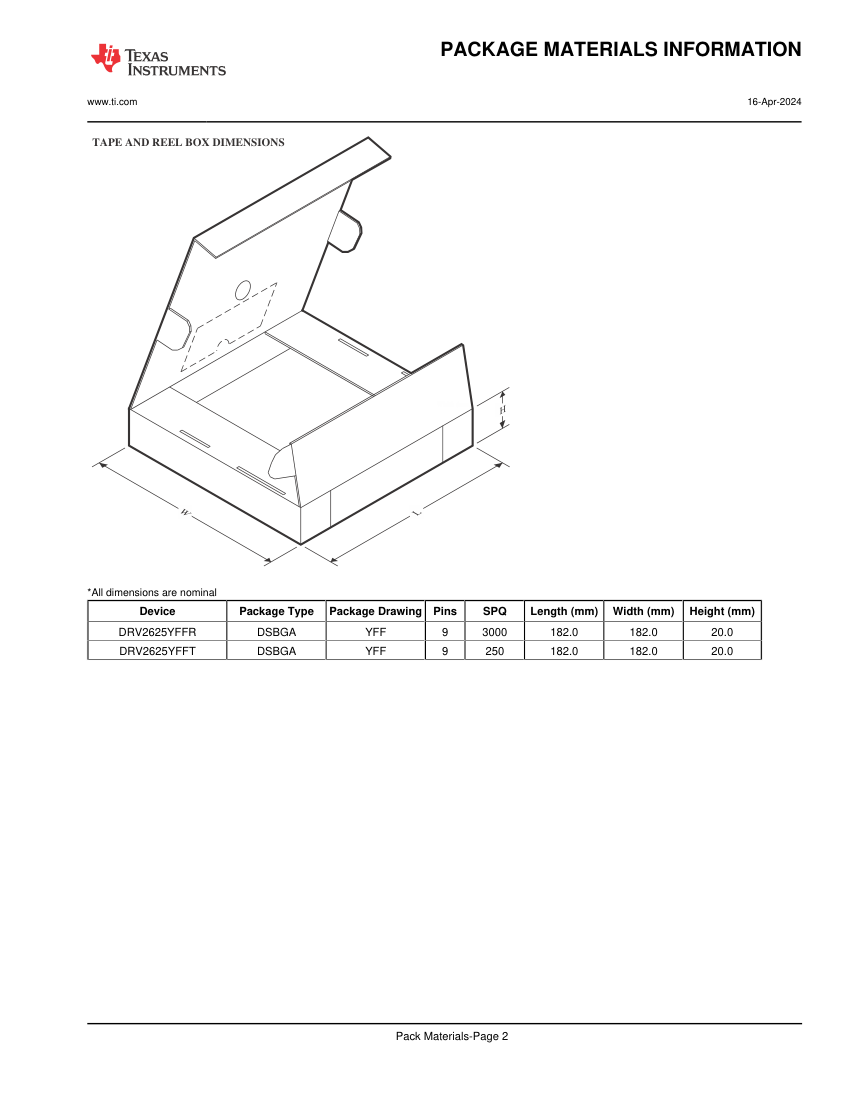
hardware/verification/placement-reference/DRV262577.png
