earlynerd/ELRS-haptics/hardware/verification/placement-reference/LTST-C19HE1WT-check.png

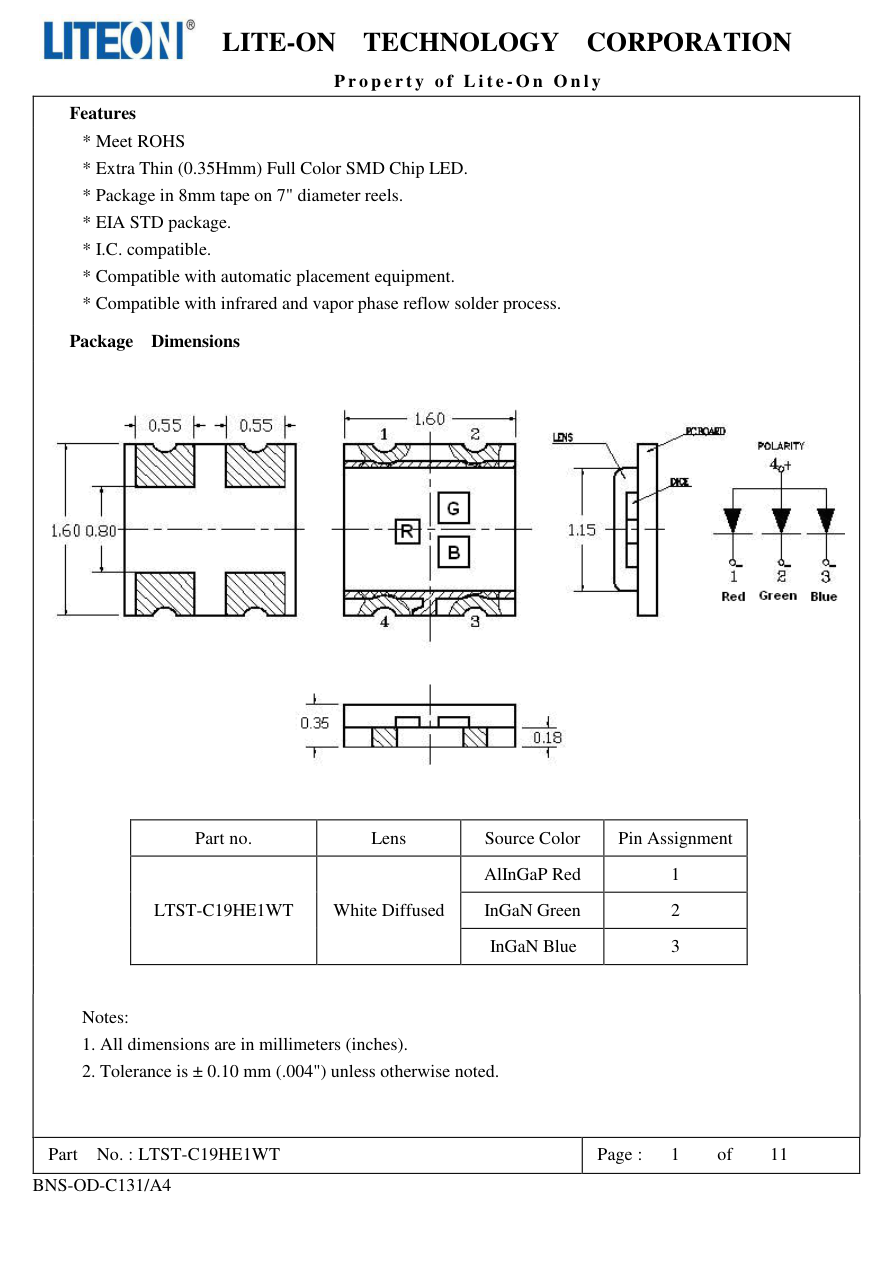
hardware/verification/placement-reference/LTST-C19HE1WT-check.png
