earlynerd/ELRS-haptics/hardware/verification/placement-reference/TPS6380235.png

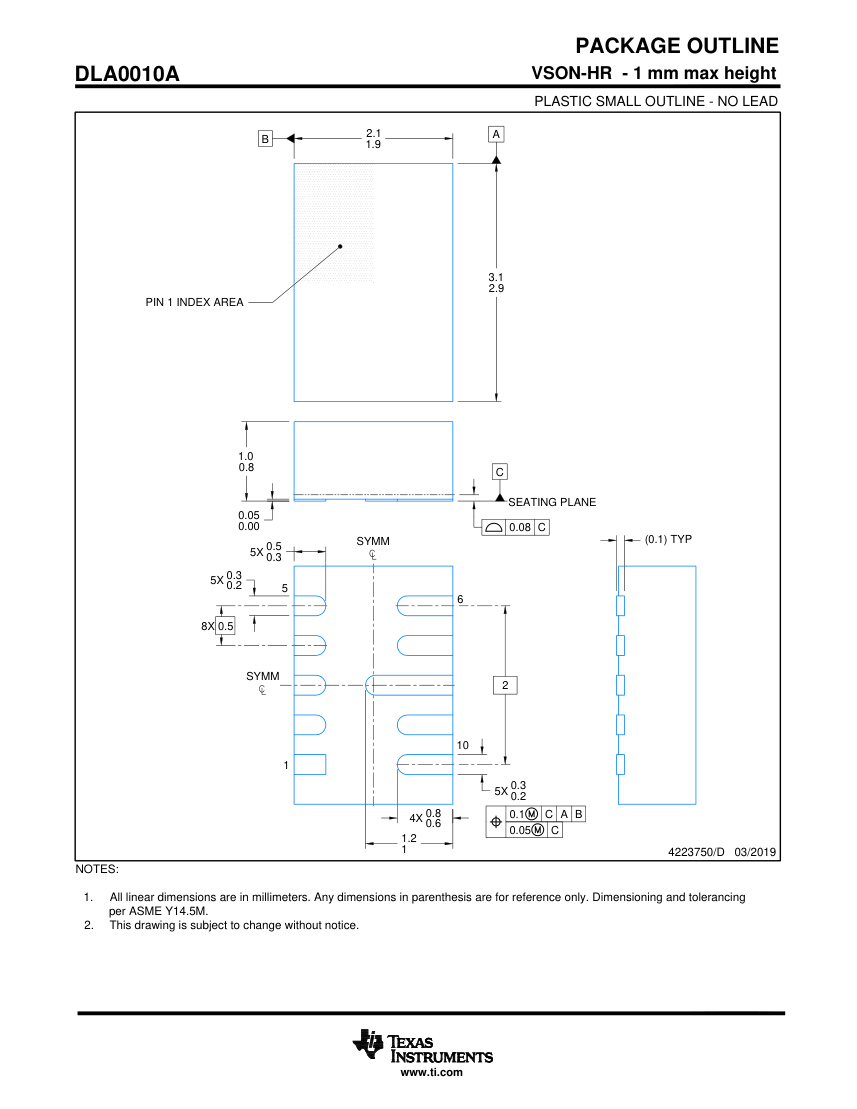
hardware/verification/placement-reference/TPS6380235.png
