earlynerd/ELRS-haptics/hardware/verification/placement-reference/TPS6380236.png

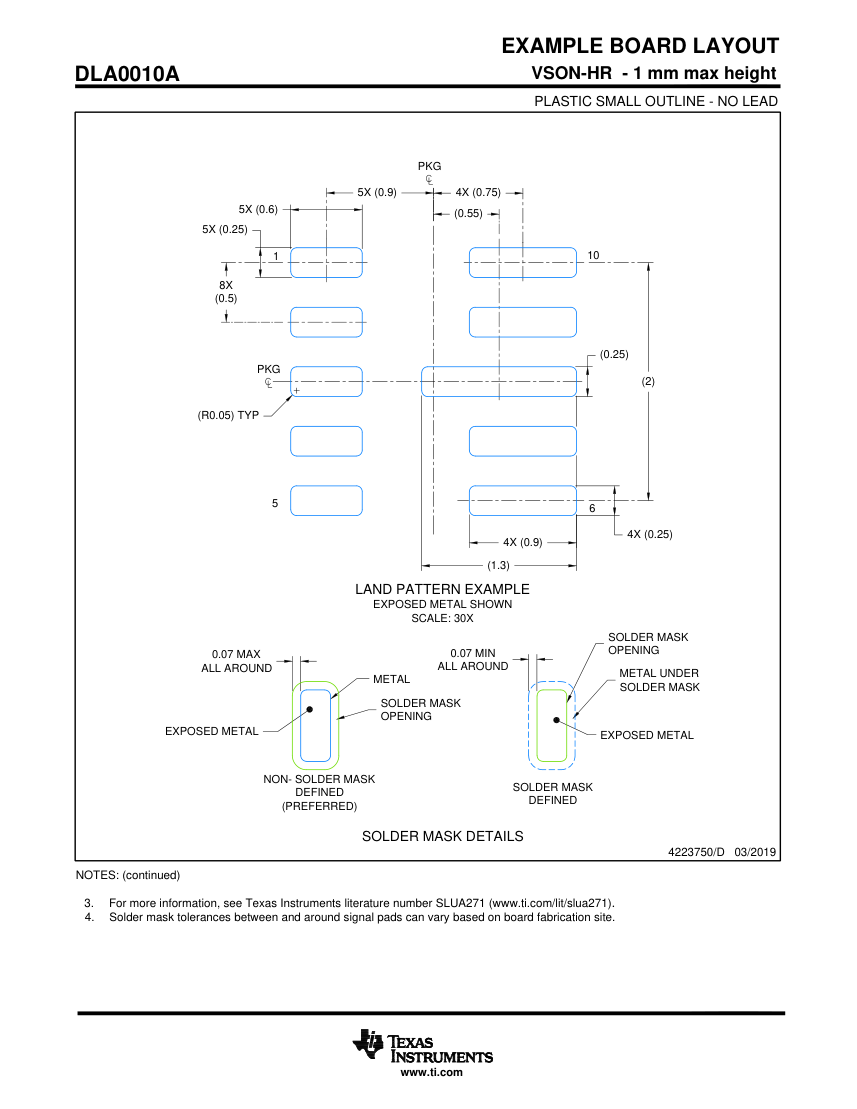
hardware/verification/placement-reference/TPS6380236.png
