earlynerd/ELRS-haptics/hardware/verification/pod-symmetry/controls.png

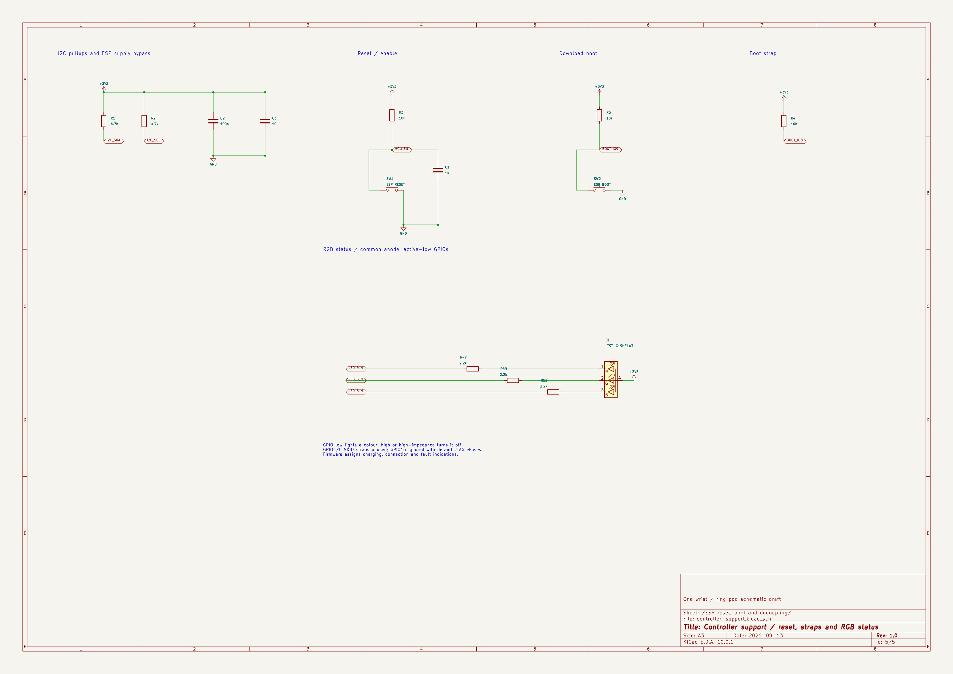
hardware/verification/pod-symmetry/controls.png
