earlynerd/ELRS-haptics/hardware/verification/pod-symmetry/power.png

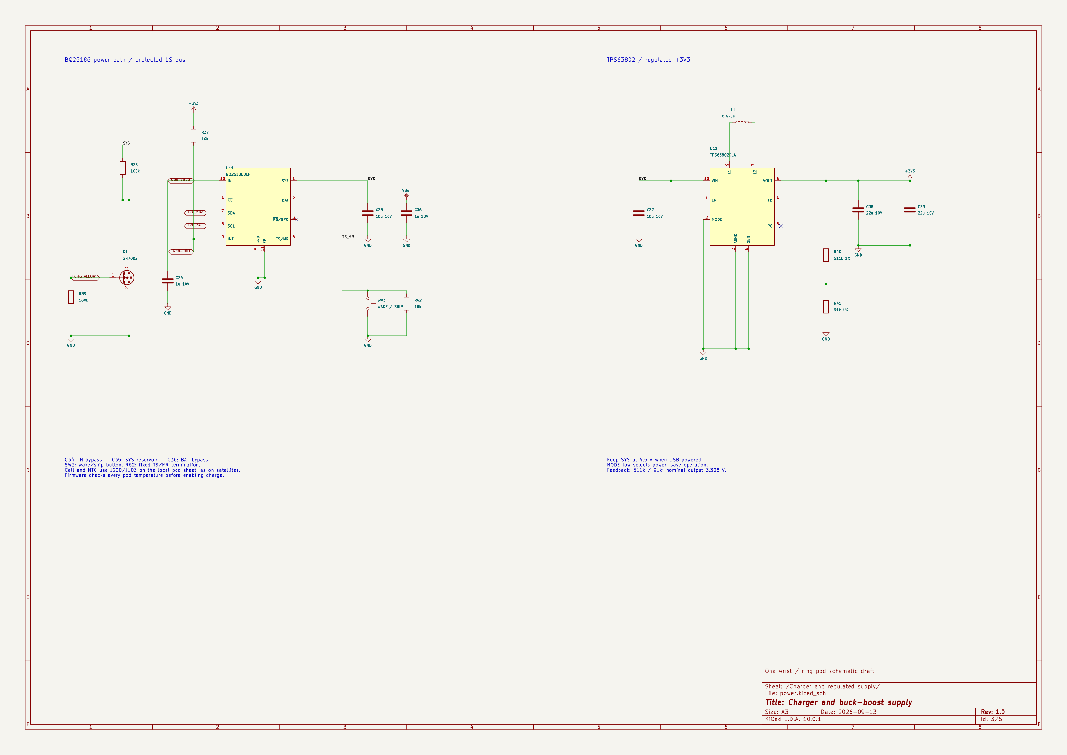
hardware/verification/pod-symmetry/power.png
