earlynerd/ELRS-haptics/hardware/verification/project-split/back.png

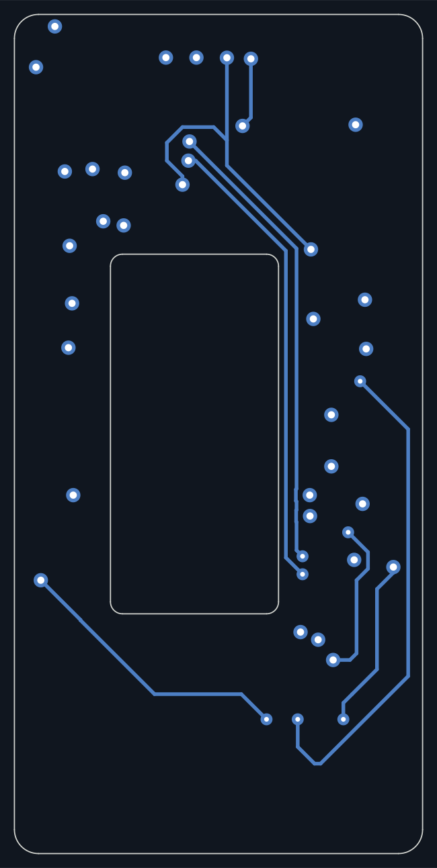
hardware/verification/project-split/back.png
