earlynerd/ELRS-haptics/hardware/verification/project-split/ground.png

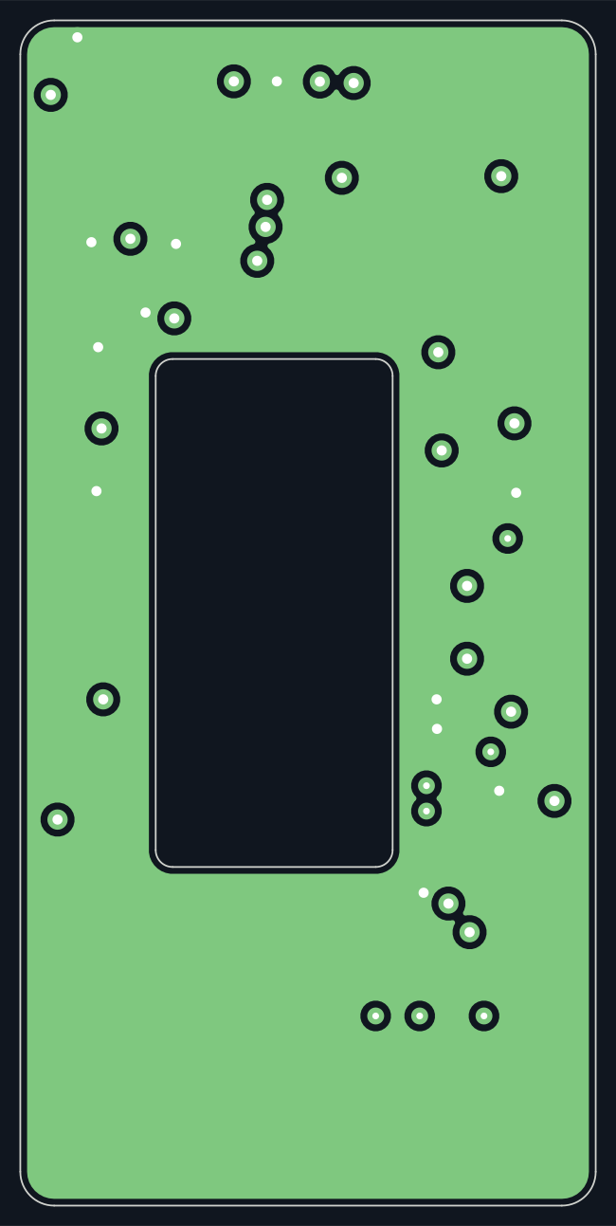
hardware/verification/project-split/ground.png
