earlynerd/ELRS-haptics/hardware/verification/project-split/main-front.png

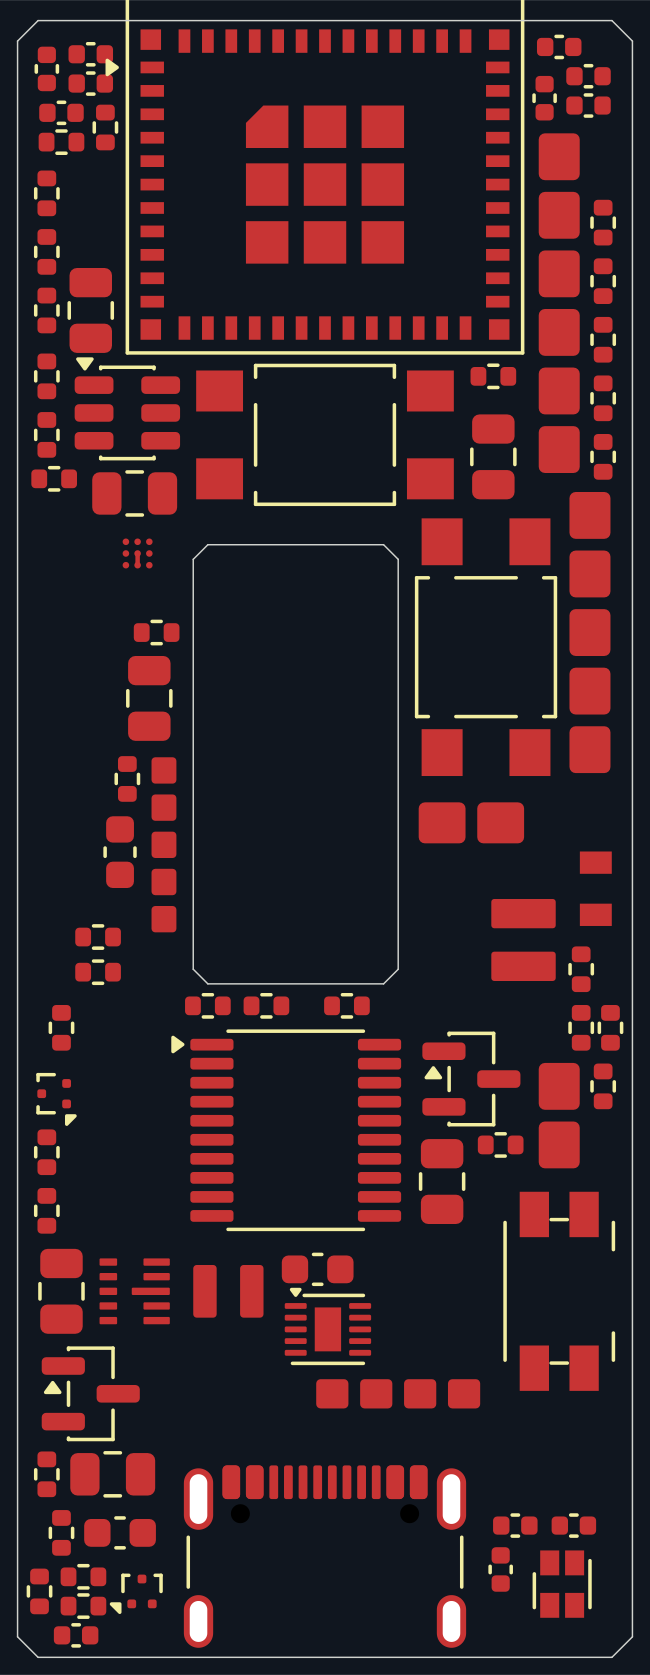
hardware/verification/project-split/main-front.png
