earlynerd/ELRS-haptics/hardware/verification/project-split/main-svg/main-Local haptic pod and harness.png

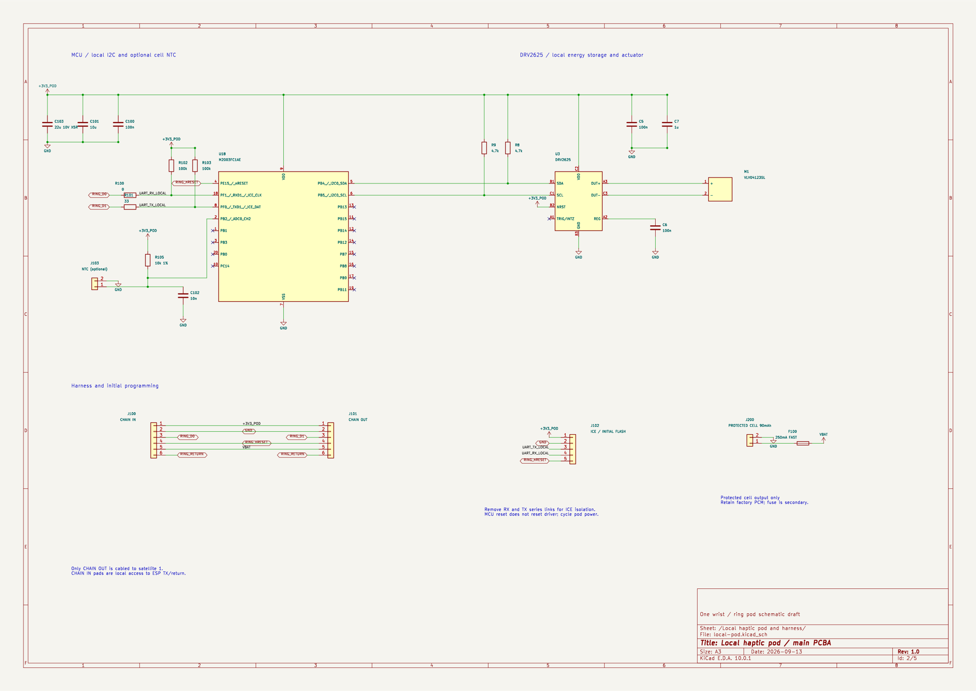
hardware/verification/project-split/main-svg/main-Local haptic pod and harness.png
