earlynerd/ELRS-haptics/hardware/verification/project-split/main-svg/main-USB-C data and power.png

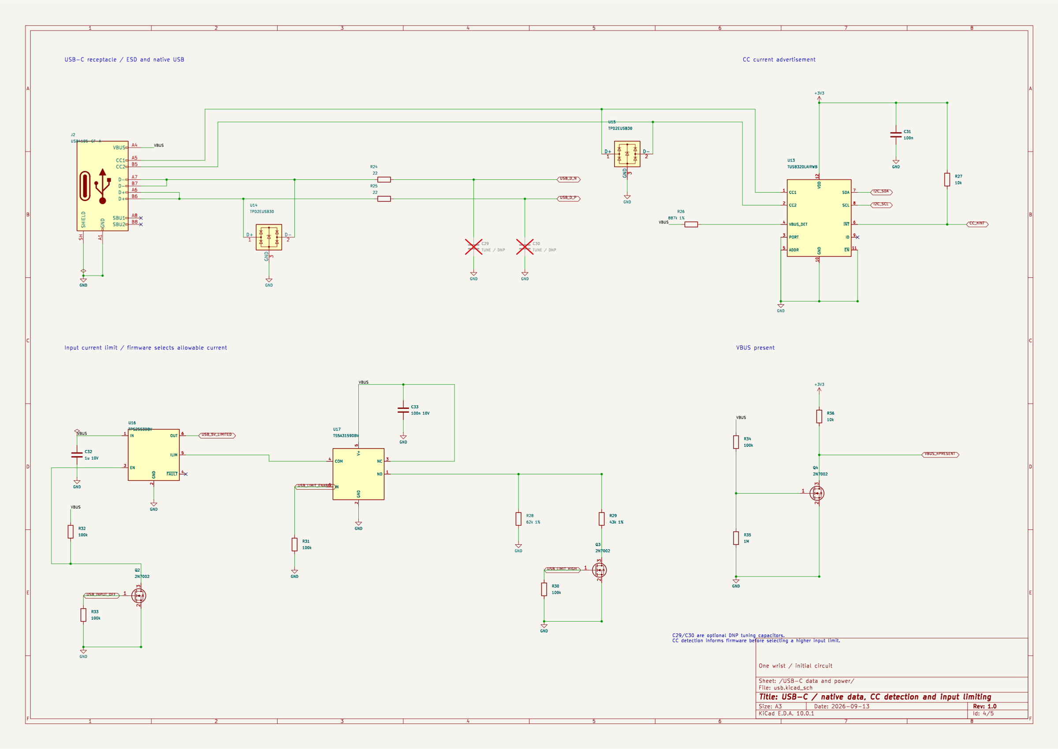
hardware/verification/project-split/main-svg/main-USB-C data and power.png
