earlynerd/ELRS-haptics/hardware/verification/project-split/main-svg/main.png

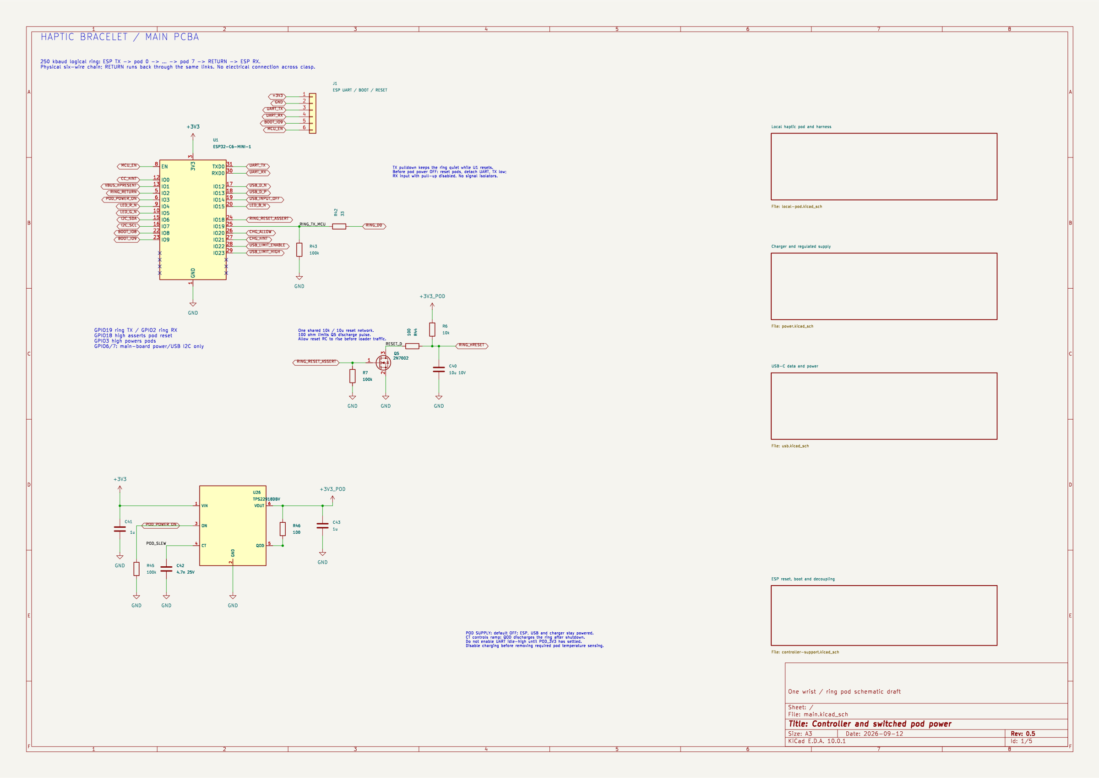
hardware/verification/project-split/main-svg/main.png
