earlynerd/ELRS-haptics/hardware/verification/project-split/power.png

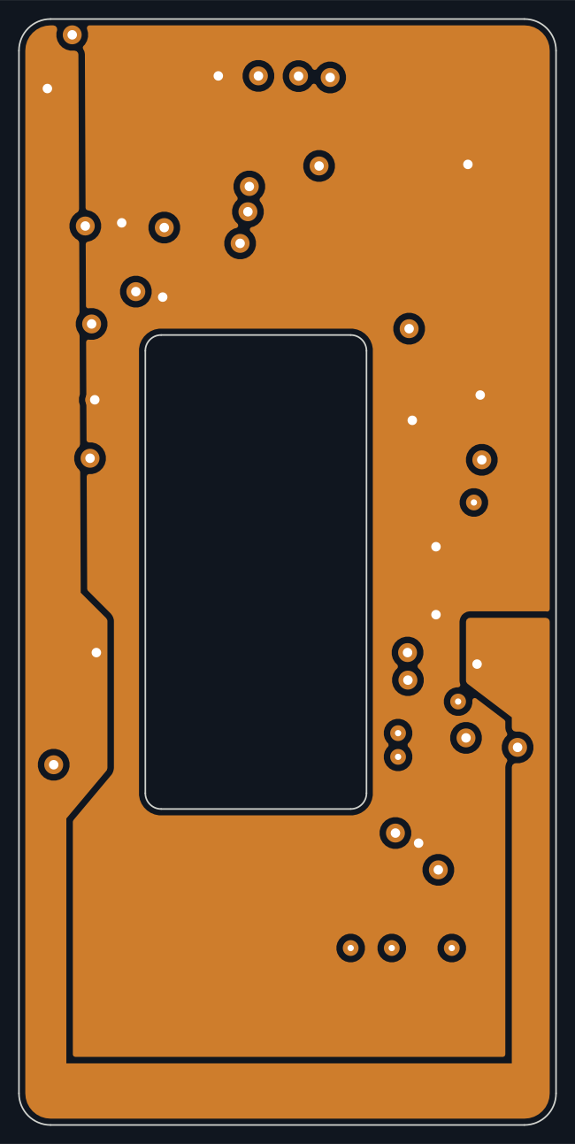
hardware/verification/project-split/power.png
