earlynerd/ELRS-haptics/hardware/verification/project-split/satellite-preview.png

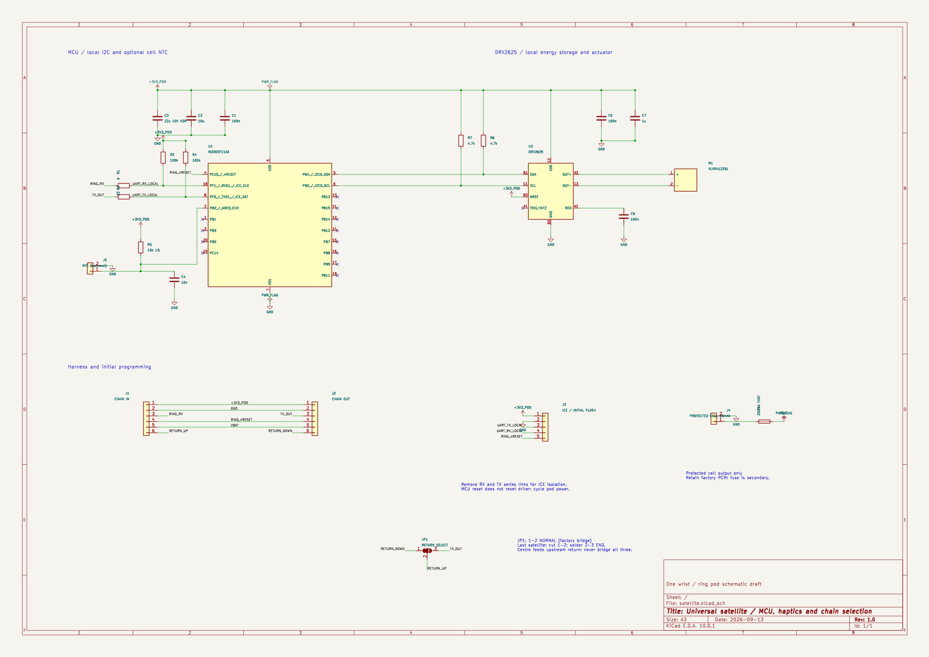
hardware/verification/project-split/satellite-preview.png
