earlynerd/ELRS-haptics/hardware/verification/project-split/top-before.png

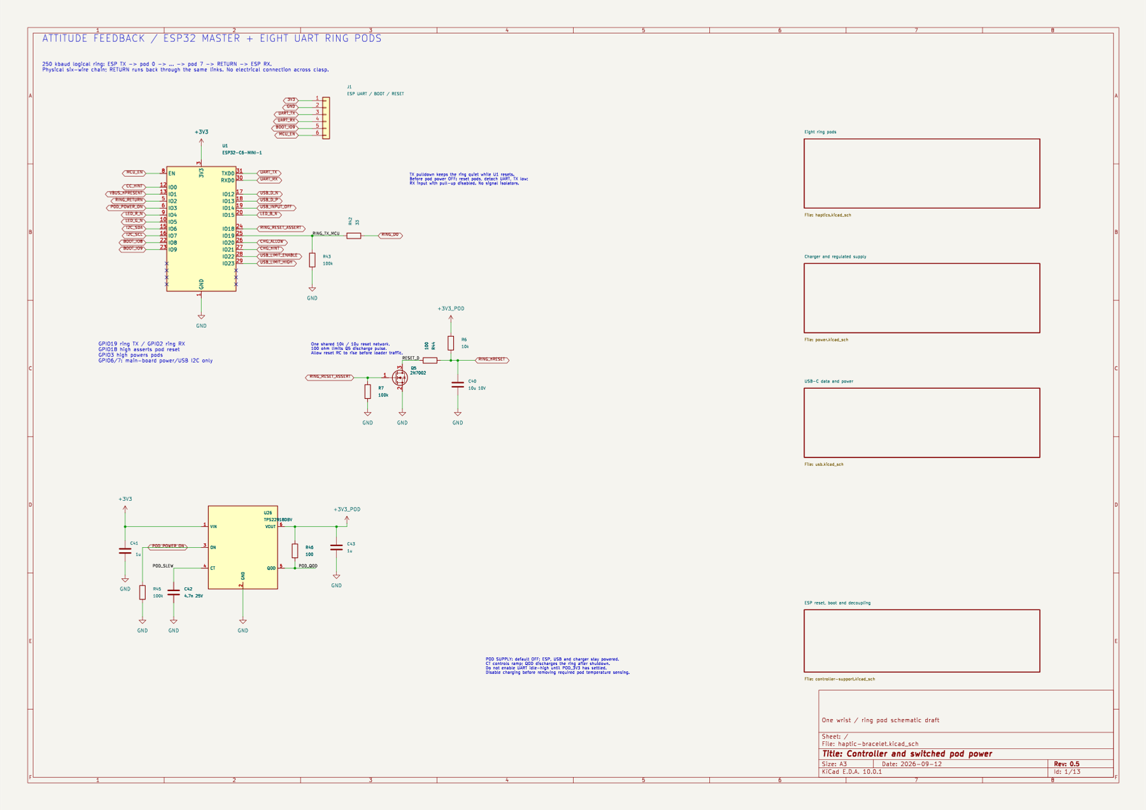
hardware/verification/project-split/top-before.png
