earlynerd/ELRS-haptics/hardware/verification/routing-v09/back.png

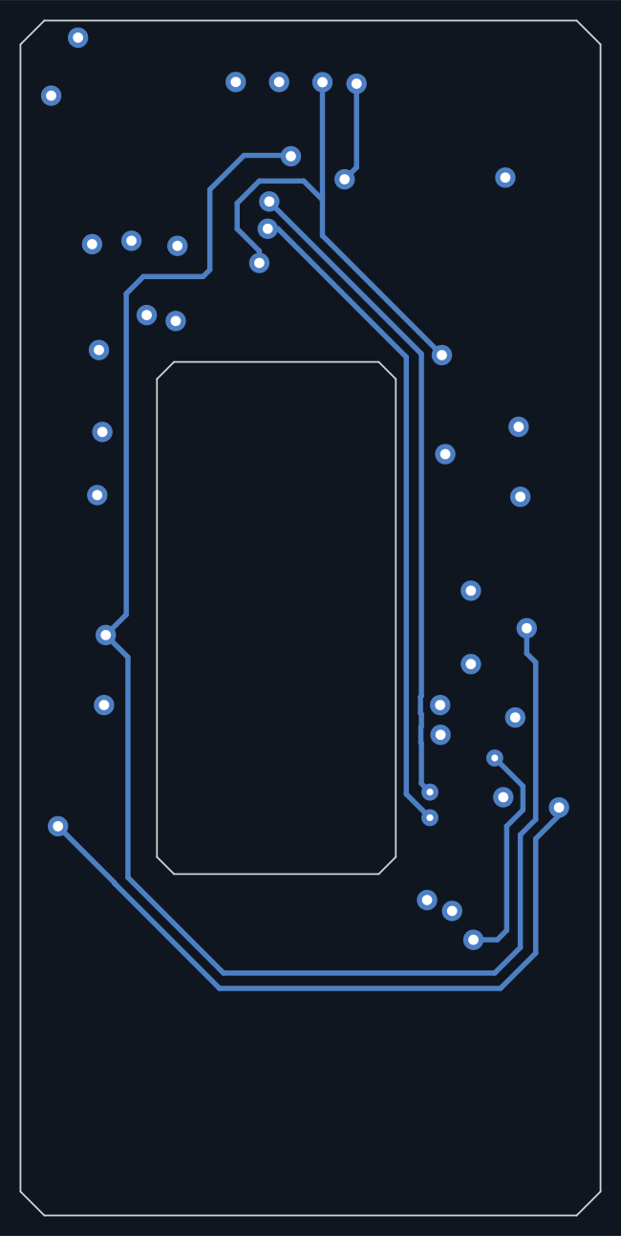
hardware/verification/routing-v09/back.png
