earlynerd/ELRS-haptics/hardware/verification/routing-v09/front.png

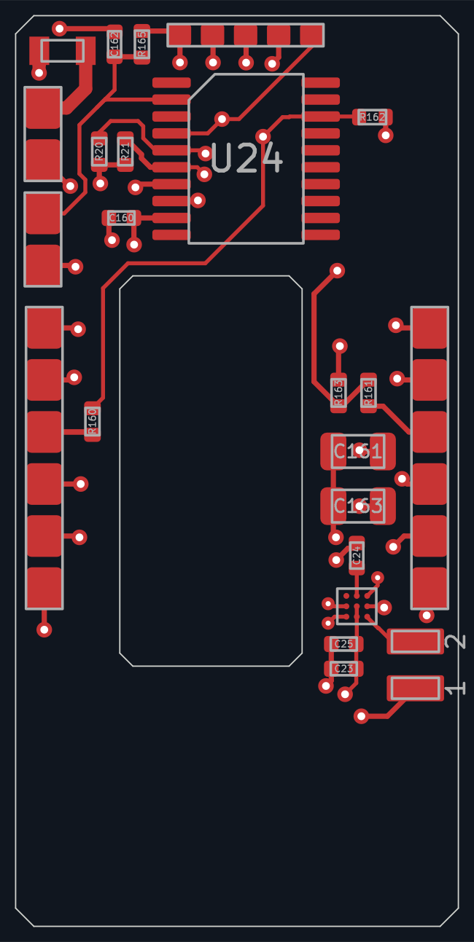
hardware/verification/routing-v09/front.png
