earlynerd/ELRS-haptics/hardware/verification/routing-v09/layers.png

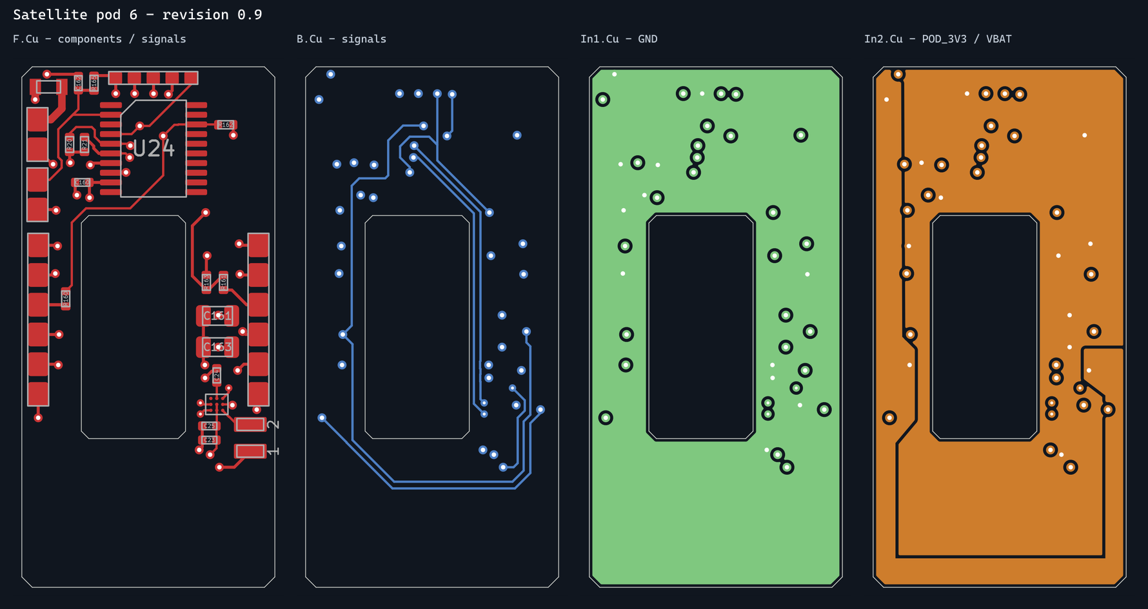
hardware/verification/routing-v09/layers.png
