earlynerd/ELRS-haptics/hardware/verification/routing/fuse-land.png

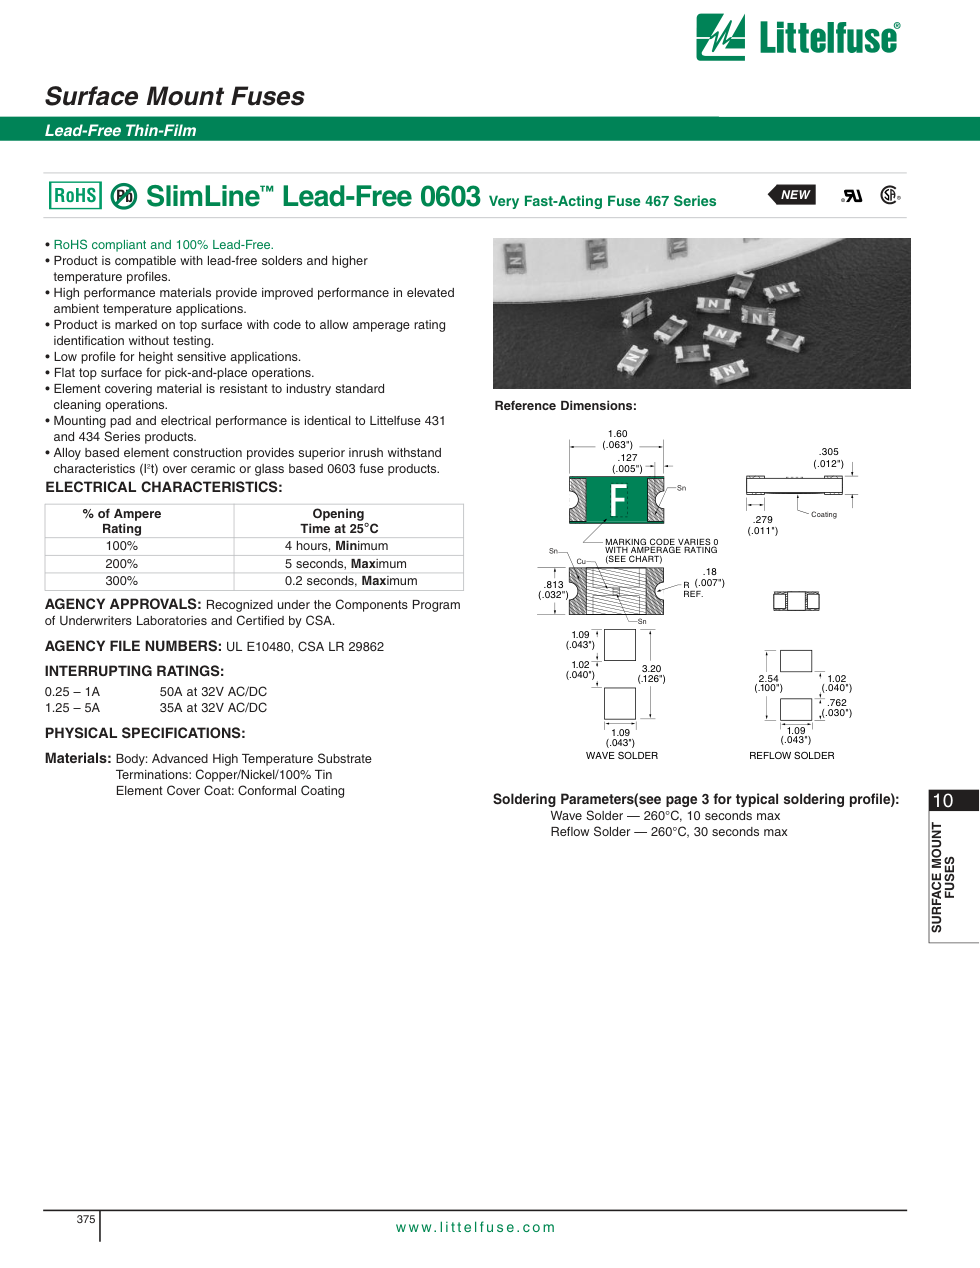
hardware/verification/routing/fuse-land.png
