earlynerd/ELRS-haptics/hardware/verification/routing/inductor-land.png

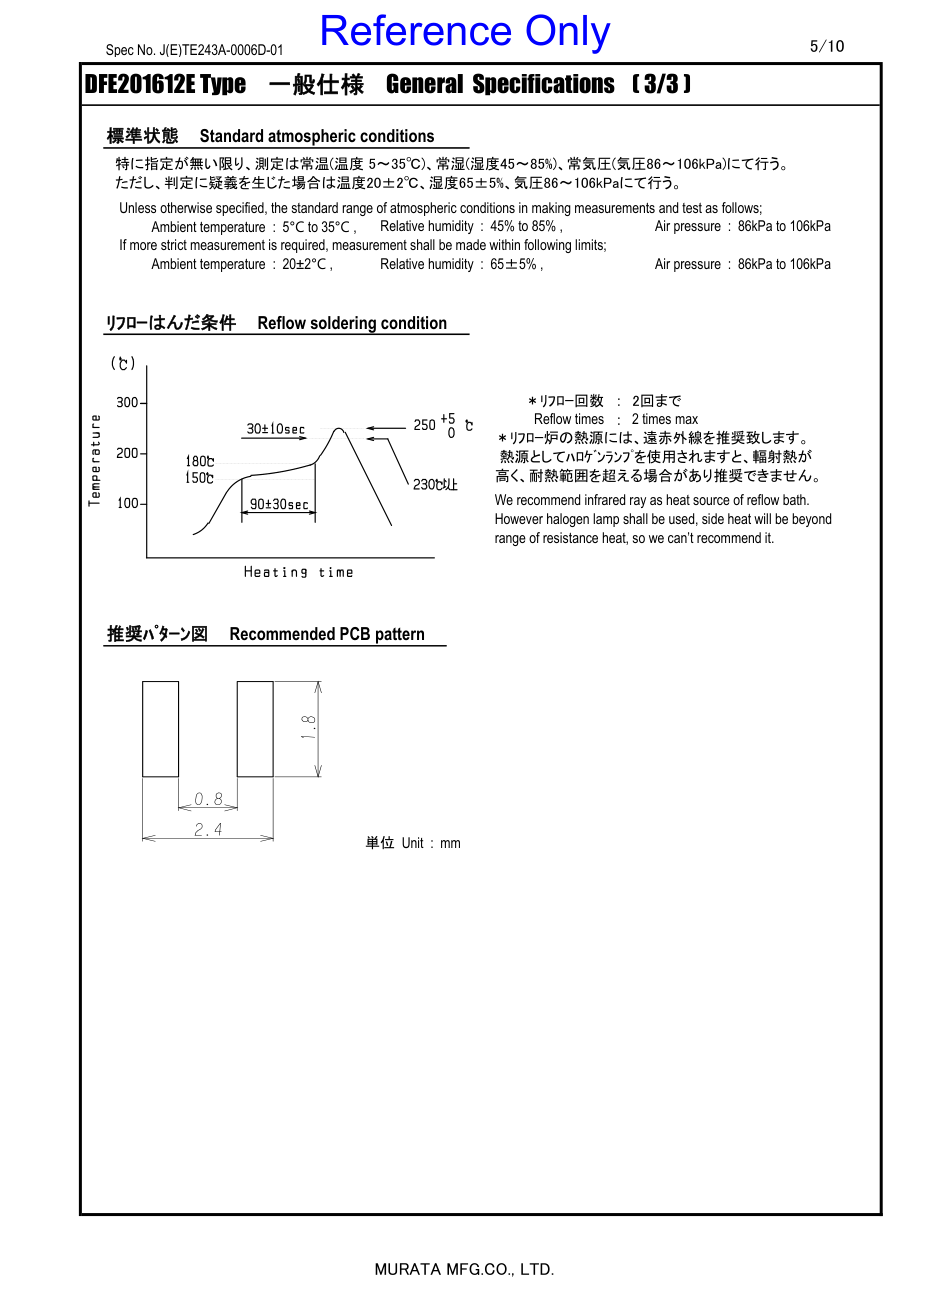
hardware/verification/routing/inductor-land.png
