earlynerd/ELRS-haptics/hardware/verification/routing/pod-1-back.png

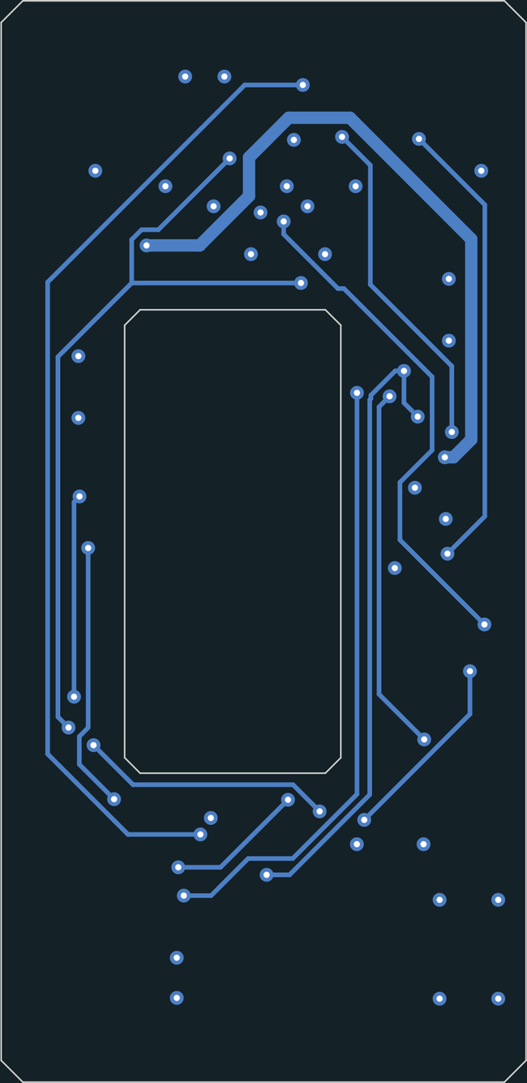
hardware/verification/routing/pod-1-back.png
