earlynerd/ELRS-haptics/hardware/verification/routing/pod-1-front.png

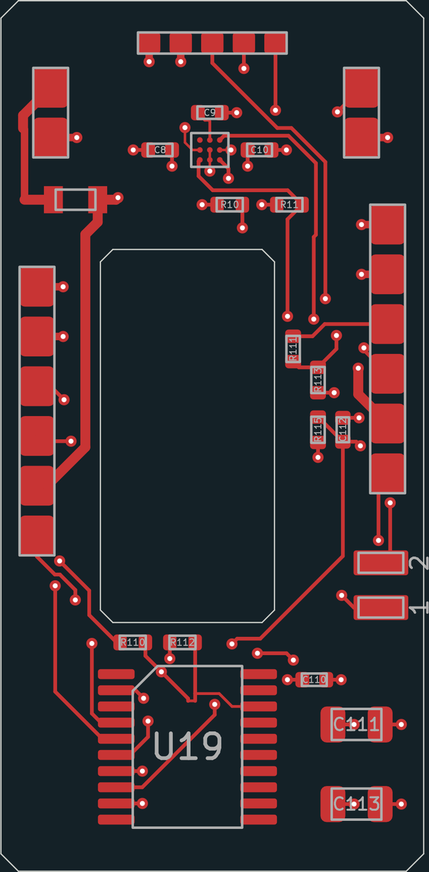
hardware/verification/routing/pod-1-front.png
