earlynerd/ELRS-haptics/hardware/verification/routing/pod-1-ground.png

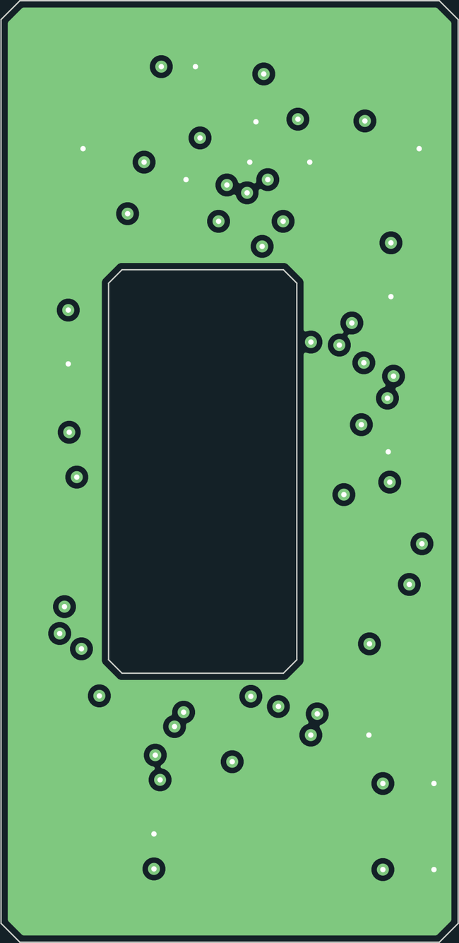
hardware/verification/routing/pod-1-ground.png
