earlynerd/ELRS-haptics/hardware/verification/routing/pod-7-power.png

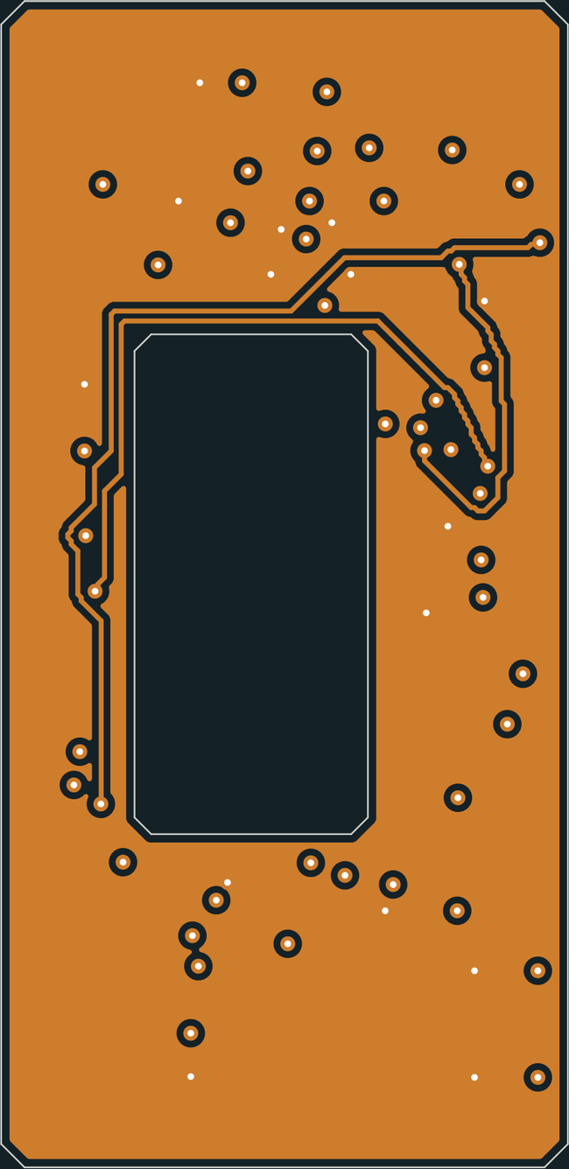
hardware/verification/routing/pod-7-power.png
