earlynerd/ELRS-haptics/hardware/verification/S82N1A-application.png

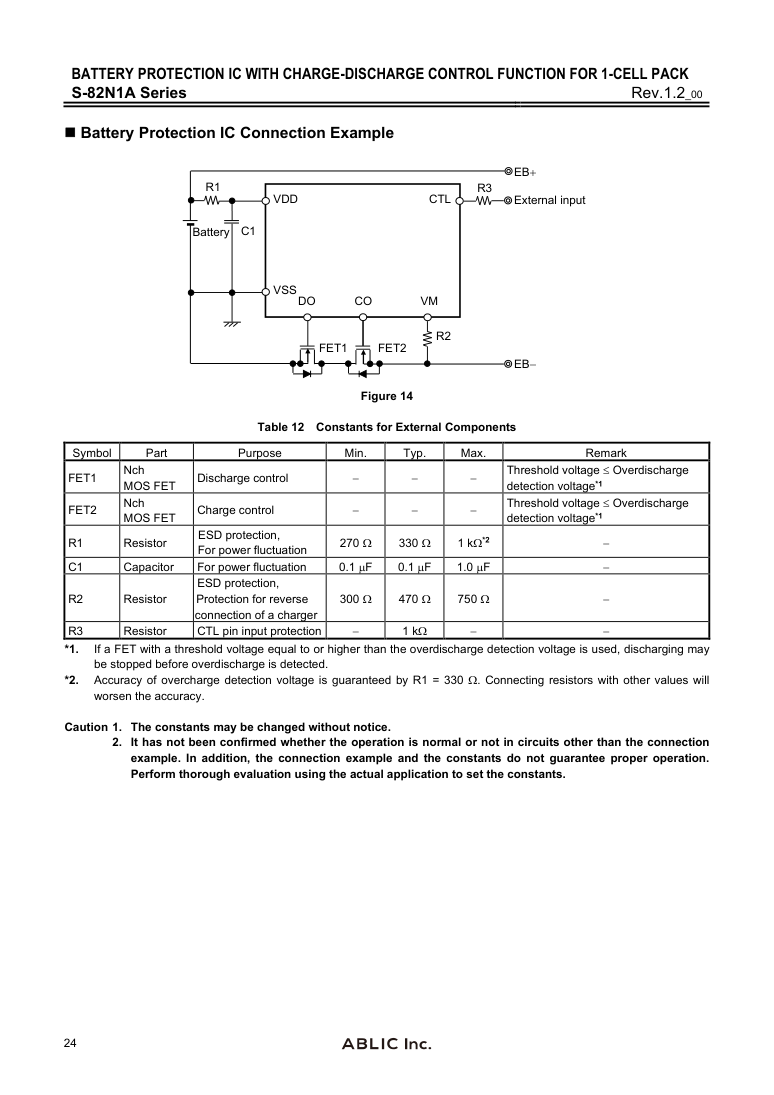
hardware/verification/S82N1A-application.png
