earlynerd/ELRS-haptics/hardware/verification/S821AA-application.png

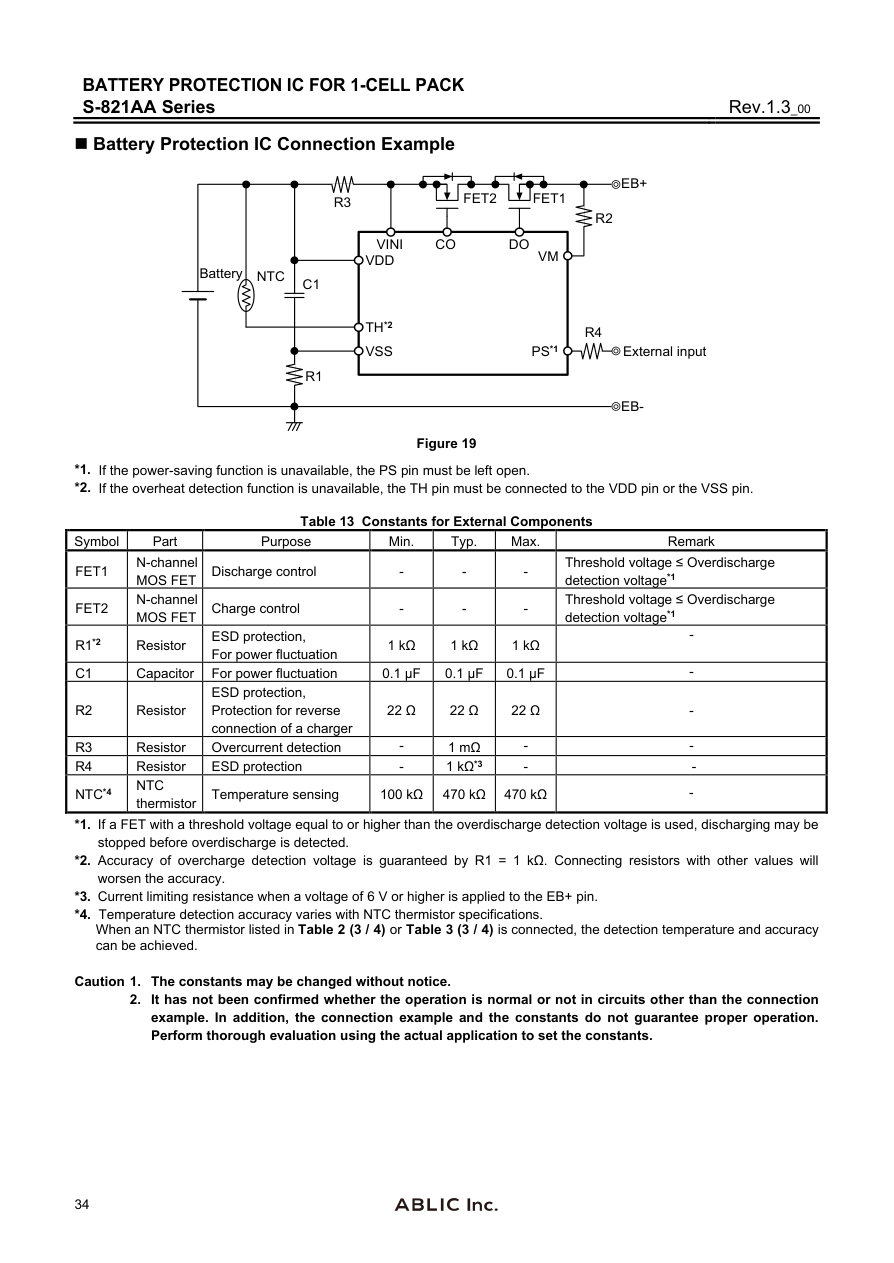
hardware/verification/S821AA-application.png
