earlynerd/ELRS-haptics/hardware/verification/S821AA-page-48.png

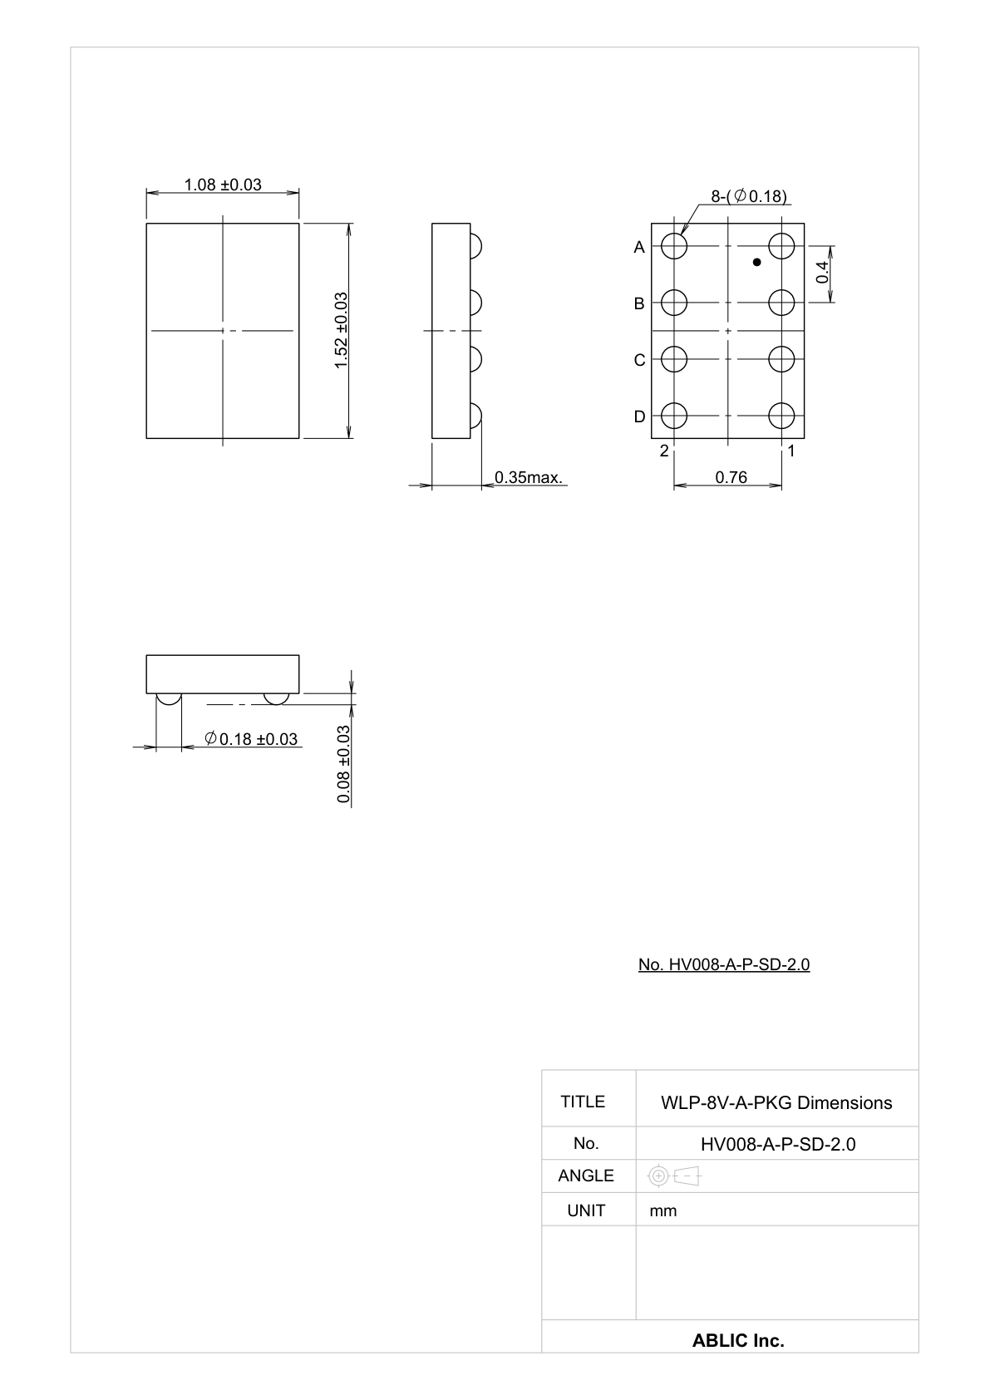
hardware/verification/S821AA-page-48.png
