earlynerd/ELRS-haptics/hardware/verification/S821AA-page-51.png

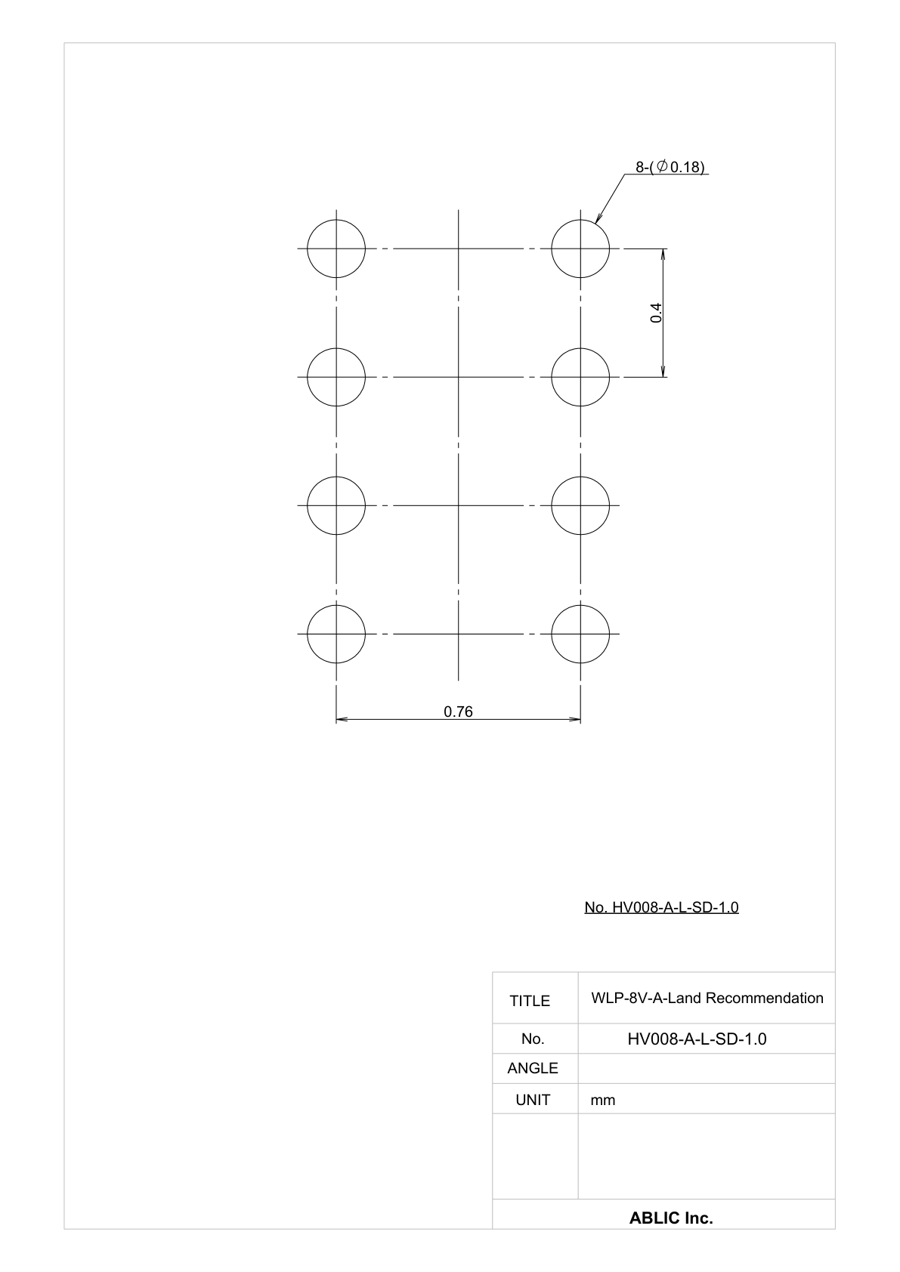
hardware/verification/S821AA-page-51.png
