earlynerd/ELRS-haptics/hardware/verification/simple-usb/usb.png

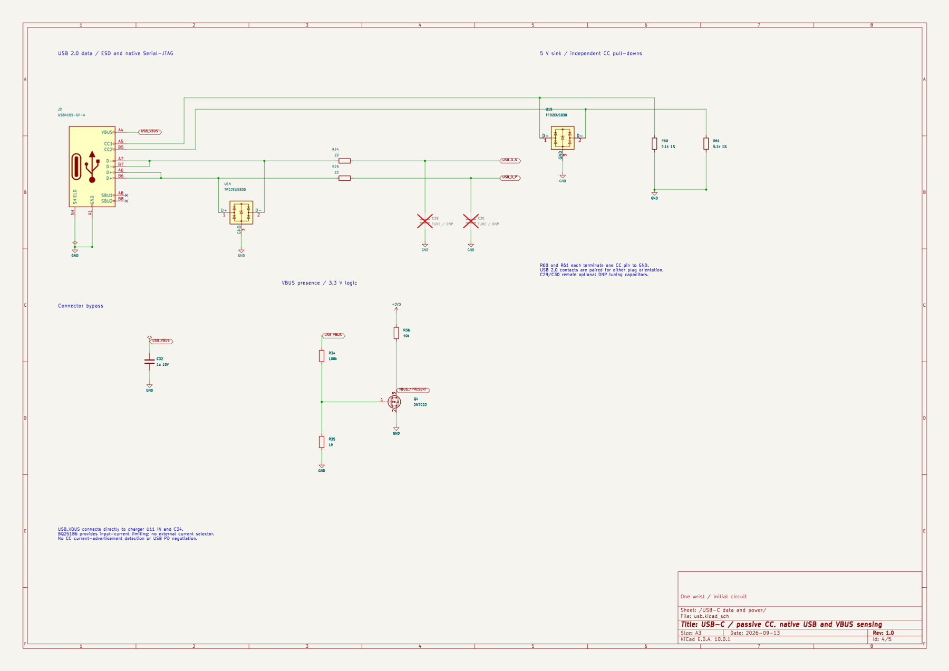
hardware/verification/simple-usb/usb.png
