earlynerd/ELRS-haptics/hardware/verification/uart-vbus-removal/main.png

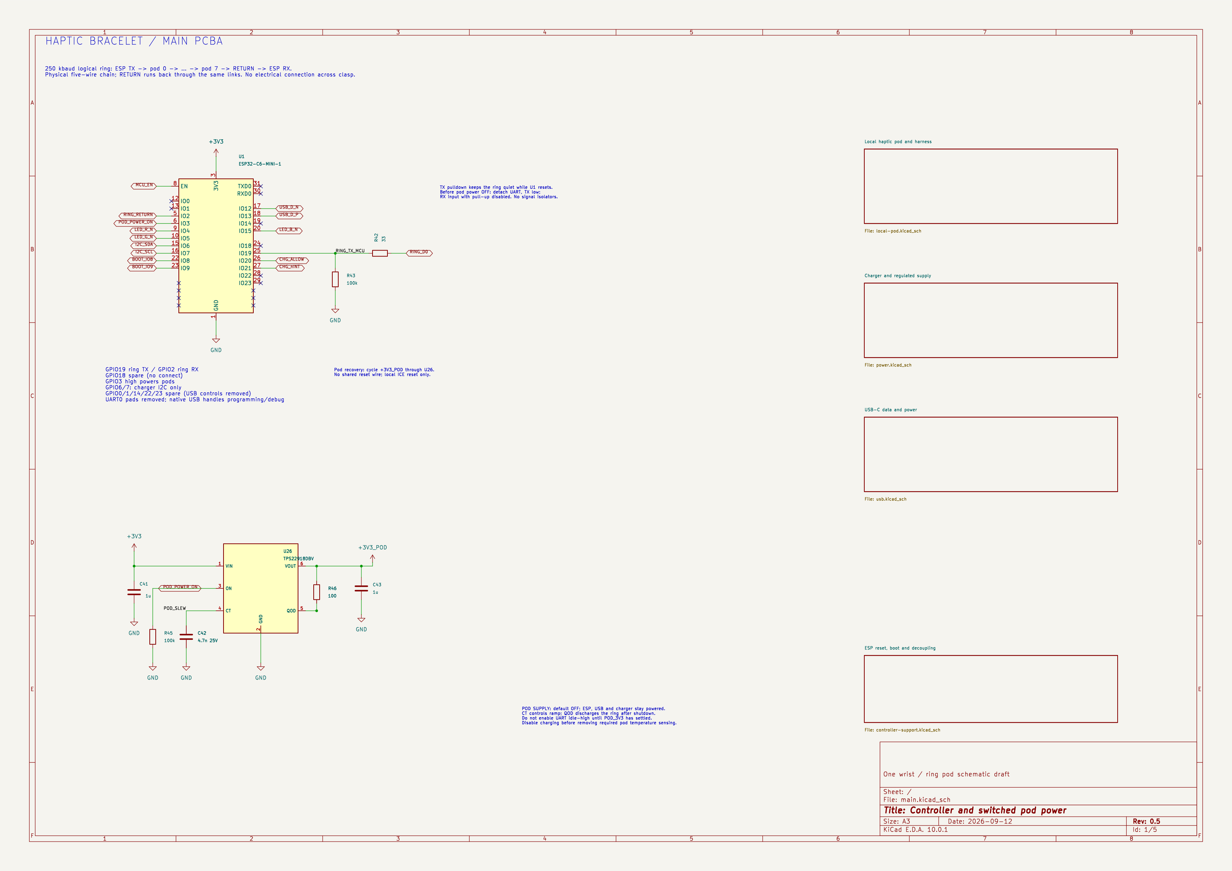
hardware/verification/uart-vbus-removal/main.png
