earlynerd/ELRS-haptics/hardware/verification/user-pod-6-20260913/front.png

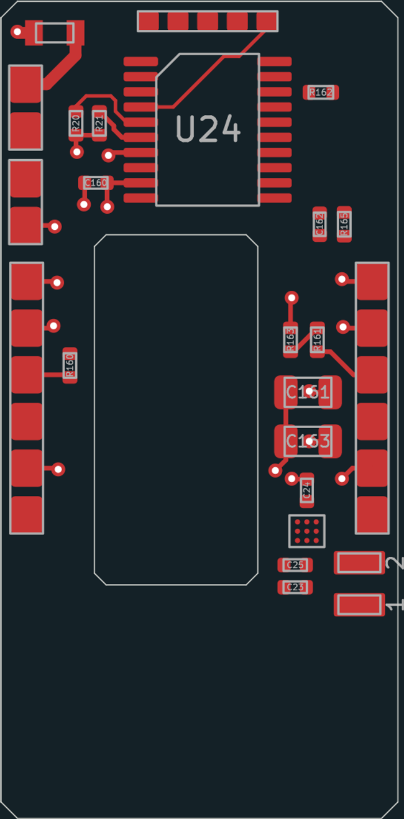
hardware/verification/user-pod-6-20260913/front.png
