earlynerd/ELRS-haptics/hardware/verification/user-pod-6-20260913/power.png

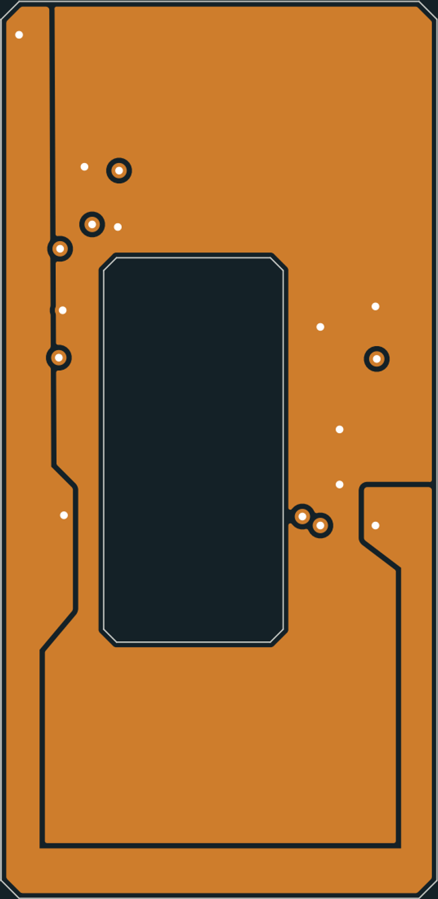
hardware/verification/user-pod-6-20260913/power.png
