earlynerd/ELRS-haptics/hardware/verification/YDL301230-pack-drawing.png

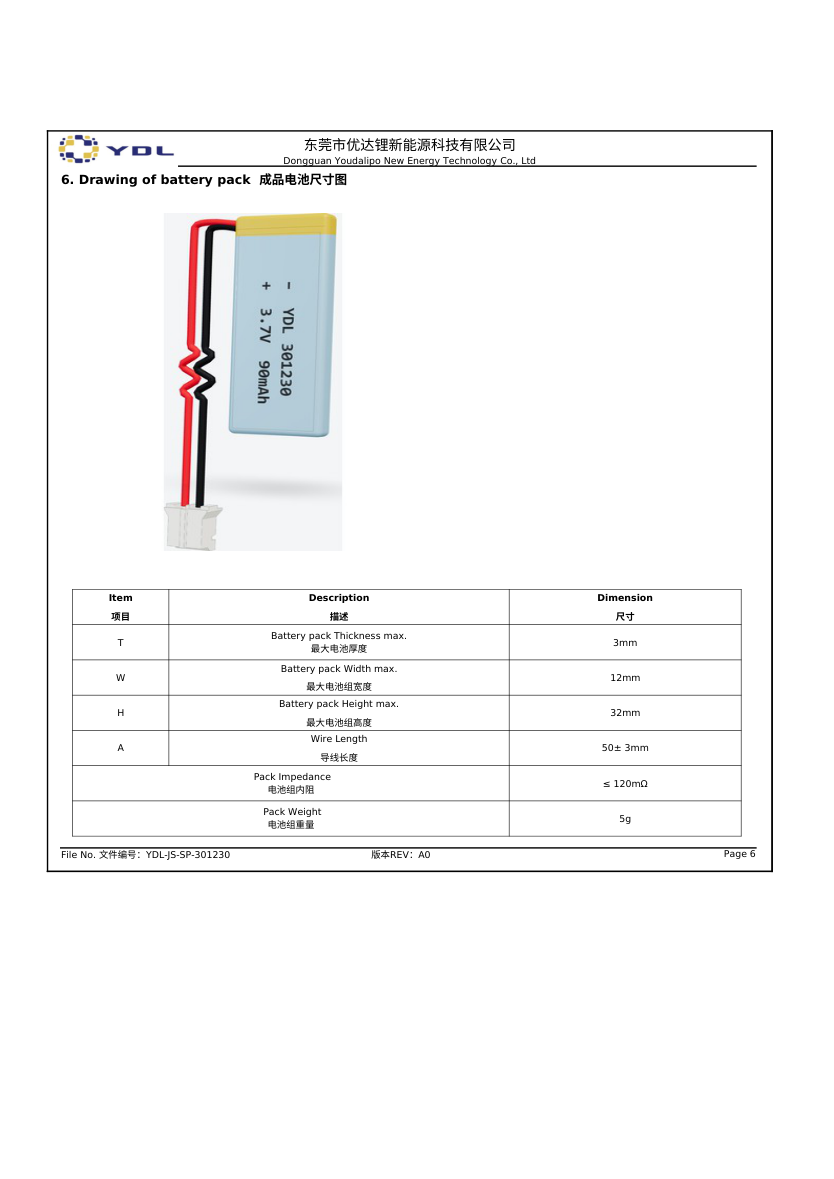
hardware/verification/YDL301230-pack-drawing.png
