earlynerd/ELRS-haptics/hardware/verification/routing-v08/merged.kicad_pcb

## KiCad design hardware/verification/routing-v08/merged.kicad_pcb (2026-09-14, an earlier design)

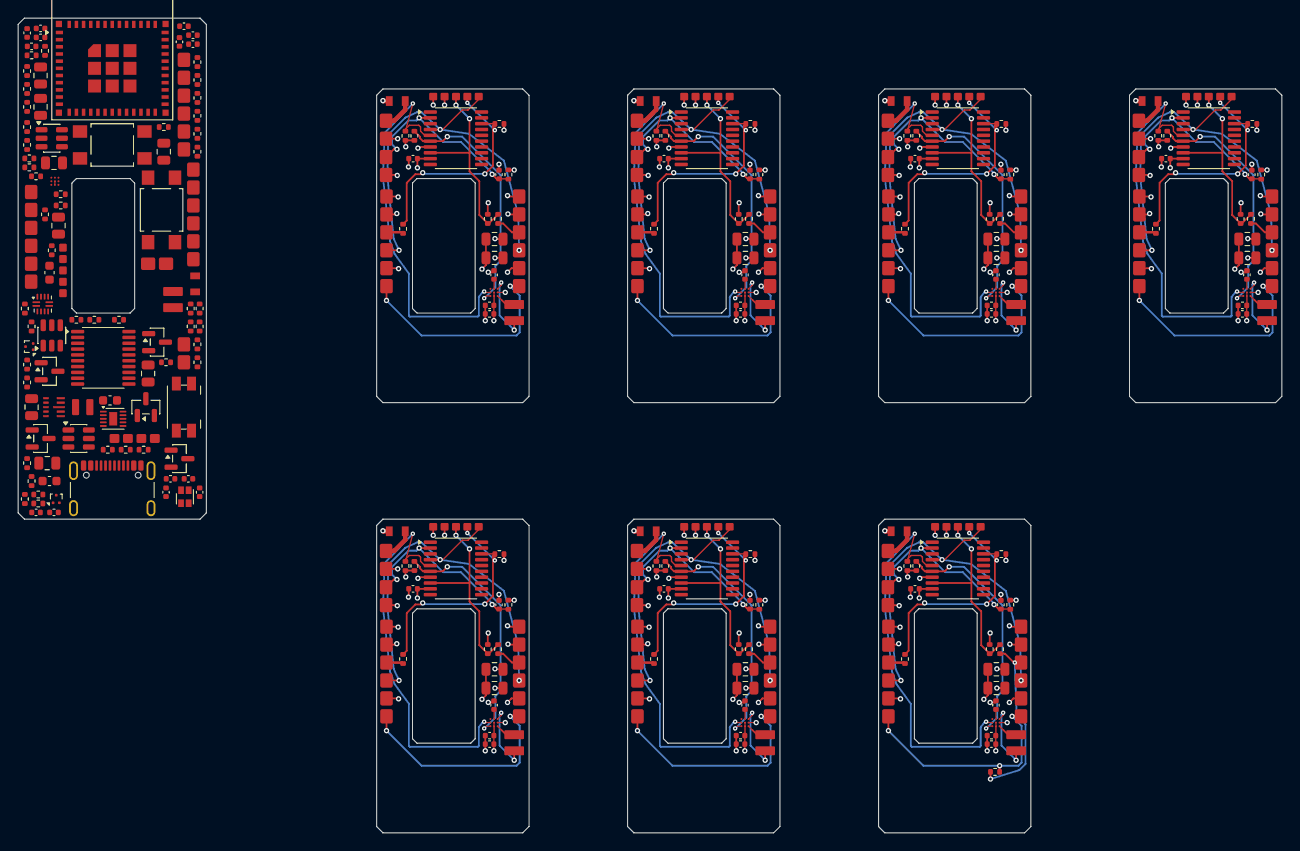
[picture p110: board merged.kicad_pcb from above]

Board: 4 copper layers, 141.0 x 90.9 mm, 261 parts (0 on the bottom side), 133 nets.

Parts:
C1, C7, C10, C13, C16, C19, C22, C25, C28, C41, C43: 1u; C_0402_1005Metric
C2, C5, C6, C8, C9, C11, C12, C14, C15, C17, C18, C20, C21, C23, C24, C26, C27, C31, C100, C110, C120, C130, C140, C150, C160, C170: 100n; C_0402_1005Metric
C3, C101, C111, C121, C131, C141, C151, C161, C171: 10u; C_0805_2012Metric
C29, C30: TUNE / DNP; C_0402_1005Metric
C32, C34, C36: 1u 10V; C_0603_1608Metric
C33: 100n 10V; C_0402_1005Metric
C35, C37, C40: 10u 10V; C_0805_2012Metric
C38, C39: 22u 10V; C_0805_2012Metric
C42: 4.7n 25V; C_0402_1005Metric
C102, C112, C122, C132, C142, C152, C162, C172: 10n; C_0402_1005Metric
C103, C113, C123, C133, C143, C153, C163, C173: 22u 10V X5R; C_0805_2012Metric
D1: LTST-C19HE1WT; LED_LiteOn_LTST-C19HE1WT
F100, F101, F102, F103, F104, F105, F106, F107: 250mA FAST; Fuse_Littelfuse_467_0603
J1: ESP UART / BOOT / RESET; WirePads_6_P2mm
J2: USB4105-GF-A; USB_C_Receptacle_GCT_USB4105-xx-A_16P_TopMnt_Horizontal
J3: VBAT BUS + NTC; WirePads_4_P1.5mm
J100, J104, J108, J112, J116, J120, J124, J128: CHAIN IN; WirePads_6_P2mm
J101, J105, J109, J113, J117, J121, J125, J129: CHAIN OUT; WirePads_6_P2mm
J102, J106, J110, J114, J118, J122, J126, J130: ICE / INITIAL FLASH; WirePads_5_P1.27mm
J103, J107, J111, J115, J119, J123, J127, J131: NTC (optional); WirePads_2_P2mm
J200, J201, J202, J203, J204, J205, J206, J207: PROTECTED CELL 90mAh; WirePads_2_P2mm
L1: 0.47uH; L_Murata_DFE201612E
M1, M2, M3, M4, M5, M6, M7, M8: VLV041235L; Vybronics_VLV041235L_FPC_Contact_Draft
Q1, Q2, Q3, Q4, Q5: 2N7002; SOT-23
R1, R2, R8, R9, R10, R11, R12, R13, R14, R15, R16, R17, R18, R19, R20, R21, R22, R23: 4.7k; R_0402_1005Metric
R3, R4, R5, R6, R27, R36, R37: 10k; R_0402_1005Metric
R7, R30, R31, R32, R33, R34, R38, R39, R43, R45, R48, R50, R52, R102, R103, R112, R113, R122, R123, R132, R133, R142, R143, R152, R153, R162, R163, R172, R173: 100k; R_0402_1005Metric
R24, R25: 22; R_0402_1005Metric
R26: 887k 1%; R_0402_1005Metric
R28: 62k 1%; R_0402_1005Metric
R29: 43k 1%; R_0402_1005Metric
R35: 1M; R_0402_1005Metric
R40: 511k 1%; R_0402_1005Metric
R41: 91k 1%; R_0402_1005Metric
R42, R101, R111, R121, R131, R141, R151, R161, R171: 33; R_0402_1005Metric
R44, R46: 100; R_0402_1005Metric
R47, R49, R51: 2.2k; R_0402_1005Metric
R53, R100, R110, R120, R130, R140, R150, R160, R170: 0; R_0402_1005Metric
R105, R115, R125, R135, R145, R155, R165, R175: 10k 1%; R_0402_1005Metric
SW1: ESP RESET; SW_SPST_TL3305A
SW2: ESP BOOT; SW_SPST_TL3305A
SW3: WAKE / SHIP; Panasonic_EVQPUJ_EVQPUA
U1: ESP32-C6-MINI-1
U3, U4, U5, U6, U7, U8, U9, U10: DRV2625; DRV2625_YFF_9_0.4mm
U11: BQ25186DLH; Texas_DLH0010A_WSON-10-1EP_2.2x2mm_P0.4mm_EP0.9x1.5mm
U12: TPS63802DLA; TPS63802_DLA0010A
U13: TUSB320LAIRWB; Texas_X2QFN-12_1.6x1.6mm_P0.4mm
U14, U15: TPD2EUSB30; Texas_DRT-3
U16: TPS2553DBV; SOT-23-6
U17: TS5A3159DBV; SOT-23-6
U18, U19, U20, U21, U22, U23, U24, U25: M2003FC1AE; TSSOP-20_4.4x6.5mm_P0.65mm
U26: TPS22918DBV; SOT-23-6

Connections:
3V3: C2.1, C3.1, C31.1, C38.1, C39.1, C41.1, D1.4, J1.1, R1.1, R2.1, R3.1, R4.1, R5.1, R27.1, R36.1, R37.1, R40.1, R48.1, R50.1, R52.1, U1.3, U12.6, U13.12, U26.1
/Charger and regulated supply/CHG_nCE: Q1.3, R38.2, U11.4
/Charger and regulated supply/PACK_TS: J3.3, SW3.1, U11.6
/Charger and regulated supply/REG_FB: R40.2, R41.1, U12.4
/Charger and regulated supply/SW_L1: L1.1, U12.9
/Charger and regulated supply/SW_L2: L1.2, U12.7
/Charger and regulated supply/SYS: C35.1, C37.1, R38.1, U11.1, U12.1, U12.10
/ESP reset, boot and decoupling/LED_B_K: D1.3, R51.2
/ESP reset, boot and decoupling/LED_G_K: D1.2, R49.2
/ESP reset, boot and decoupling/LED_R_K: D1.1, R47.2
/Eight ring pods/Pod 0 / U18/CELL_POS: F100.1, J200.1
/Eight ring pods/Pod 0 / U18/CELL_TEMP: C102.1, J103.1, R105.2, U18.2
/Eight ring pods/Pod 0 / U18/DRV_REG: C6.1, U3.A2
/Eight ring pods/Pod 0 / U18/LOCAL_SCL: R9.2, U3.C1, U18.6
/Eight ring pods/Pod 0 / U18/LOCAL_SDA: R8.2, U3.B1, U18.5
/Eight ring pods/Pod 0 / U18/LRA_N: M1.2, U3.C3
/Eight ring pods/Pod 0 / U18/LRA_P: M1.1, U3.A3
/Eight ring pods/Pod 0 / U18/UART_RX_LOCAL: J102.4, R100.2, R102.2, U18.18
/Eight ring pods/Pod 0 / U18/UART_TX_LOCAL: J102.3, R101.1, R103.2, U18.8
/Eight ring pods/Pod 1 / U19/CELL_POS: F101.1, J201.1
/Eight ring pods/Pod 1 / U19/CELL_TEMP: C112.1, J107.1, R115.2, U19.2
/Eight ring pods/Pod 1 / U19/DRV_REG: C9.1, U4.A2
/Eight ring pods/Pod 1 / U19/LOCAL_SCL: R11.2, U4.C1, U19.6
/Eight ring pods/Pod 1 / U19/LOCAL_SDA: R10.2, U4.B1, U19.5
/Eight ring pods/Pod 1 / U19/LRA_N: M2.2, U4.C3
/Eight ring pods/Pod 1 / U19/LRA_P: M2.1, U4.A3
/Eight ring pods/Pod 1 / U19/UART_RX_LOCAL: J106.4, R110.2, R112.2, U19.18
/Eight ring pods/Pod 1 / U19/UART_TX_LOCAL: J106.3, R111.1, R113.2, U19.8
/Eight ring pods/Pod 2 / U20/CELL_POS: F102.1, J202.1
/Eight ring pods/Pod 2 / U20/CELL_TEMP: C122.1, J111.1, R125.2, U20.2
/Eight ring pods/Pod 2 / U20/DRV_REG: C12.1, U5.A2
/Eight ring pods/Pod 2 / U20/LOCAL_SCL: R13.2, U5.C1, U20.6
/Eight ring pods/Pod 2 / U20/LOCAL_SDA: R12.2, U5.B1, U20.5
/Eight ring pods/Pod 2 / U20/LRA_N: M3.2, U5.C3
/Eight ring pods/Pod 2 / U20/LRA_P: M3.1, U5.A3
/Eight ring pods/Pod 2 / U20/UART_RX_LOCAL: J110.4, R120.2, R122.2, U20.18
/Eight ring pods/Pod 2 / U20/UART_TX_LOCAL: J110.3, R121.1, R123.2, U20.8
/Eight ring pods/Pod 3 / U21/CELL_POS: F103.1, J203.1
/Eight ring pods/Pod 3 / U21/CELL_TEMP: C132.1, J115.1, R135.2, U21.2
/Eight ring pods/Pod 3 / U21/DRV_REG: C15.1, U6.A2
/Eight ring pods/Pod 3 / U21/LOCAL_SCL: R15.2, U6.C1, U21.6
/Eight ring pods/Pod 3 / U21/LOCAL_SDA: R14.2, U6.B1, U21.5
/Eight ring pods/Pod 3 / U21/LRA_N: M4.2, U6.C3
/Eight ring pods/Pod 3 / U21/LRA_P: M4.1, U6.A3
/Eight ring pods/Pod 3 / U21/UART_RX_LOCAL: J114.4, R130.2, R132.2, U21.18
/Eight ring pods/Pod 3 / U21/UART_TX_LOCAL: J114.3, R131.1, R133.2, U21.8
/Eight ring pods/Pod 4 / U22/CELL_POS: F104.1, J204.1
/Eight ring pods/Pod 4 / U22/CELL_TEMP: C142.1, J119.1, R145.2, U22.2
/Eight ring pods/Pod 4 / U22/DRV_REG: C18.1, U7.A2
/Eight ring pods/Pod 4 / U22/LOCAL_SCL: R17.2, U7.C1, U22.6
/Eight ring pods/Pod 4 / U22/LOCAL_SDA: R16.2, U7.B1, U22.5
/Eight ring pods/Pod 4 / U22/LRA_N: M5.2, U7.C3
/Eight ring pods/Pod 4 / U22/LRA_P: M5.1, U7.A3
/Eight ring pods/Pod 4 / U22/UART_RX_LOCAL: J118.4, R140.2, R142.2, U22.18
/Eight ring pods/Pod 4 / U22/UART_TX_LOCAL: J118.3, R141.1, R143.2, U22.8
/Eight ring pods/Pod 5 / U23/CELL_POS: F105.1, J205.1
/Eight ring pods/Pod 5 / U23/CELL_TEMP: C152.1, J123.1, R155.2, U23.2
/Eight ring pods/Pod 5 / U23/DRV_REG: C21.1, U8.A2
/Eight ring pods/Pod 5 / U23/LOCAL_SCL: R19.2, U8.C1, U23.6
/Eight ring pods/Pod 5 / U23/LOCAL_SDA: R18.2, U8.B1, U23.5
/Eight ring pods/Pod 5 / U23/LRA_N: M6.2, U8.C3
/Eight ring pods/Pod 5 / U23/LRA_P: M6.1, U8.A3
/Eight ring pods/Pod 5 / U23/UART_RX_LOCAL: J122.4, R150.2, R152.2, U23.18
/Eight ring pods/Pod 5 / U23/UART_TX_LOCAL: J122.3, R151.1, R153.2, U23.8
/Eight ring pods/Pod 6 / U24/CELL_POS: F106.1, J206.1
/Eight ring pods/Pod 6 / U24/CELL_TEMP: C162.1, J127.1, R165.2, U24.2
/Eight ring pods/Pod 6 / U24/DRV_REG: C24.1, U9.A2
/Eight ring pods/Pod 6 / U24/LOCAL_SCL: R21.2, U9.C1, U24.6
/Eight ring pods/Pod 6 / U24/LOCAL_SDA: R20.2, U9.B1, U24.5
/Eight ring pods/Pod 6 / U24/LRA_N: M7.2, U9.C3
/Eight ring pods/Pod 6 / U24/LRA_P: M7.1, U9.A3
/Eight ring pods/Pod 6 / U24/UART_RX_LOCAL: J126.4, R160.2, R162.2, U24.18
/Eight ring pods/Pod 6 / U24/UART_TX_LOCAL: J126.3, R161.1, R163.2, U24.8
/Eight ring pods/Pod 7 / U25/CELL_POS: F107.1, J207.1
/Eight ring pods/Pod 7 / U25/CELL_TEMP: C172.1, J131.1, R175.2, U25.2
/Eight ring pods/Pod 7 / U25/DRV_REG: C27.1, U10.A2
/Eight ring pods/Pod 7 / U25/LOCAL_SCL: R23.2, U10.C1, U25.6
/Eight ring pods/Pod 7 / U25/LOCAL_SDA: R22.2, U10.B1, U25.5
/Eight ring pods/Pod 7 / U25/LRA_N: M8.2, U10.C3
/Eight ring pods/Pod 7 / U25/LRA_P: M8.1, U10.A3
/Eight ring pods/Pod 7 / U25/UART_RX_LOCAL: J130.4, R170.2, R172.2, U25.18
/Eight ring pods/Pod 7 / U25/UART_TX_LOCAL: J130.3, R171.1, R173.2, U25.8
/POD_QOD: R46.2, U26.5
/POD_SLEW: C42.1, U26.4
/RESET_D: Q5.3, R44.2
/RING_TX_MCU: R42.1, R43.1, U1.25
/USB-C data and power/CC1: J2.A5, U13.1, U15.1
/USB-C data and power/CC2: J2.B5, U13.2, U15.2
/USB-C data and power/CC_VBUS_DET: R26.2, U13.4
/USB-C data and power/ILIM_HIGH_D: Q3.3, R29.2
/USB-C data and power/ILIM_R: R28.1, R29.1, U17.1
/USB-C data and power/ILIM_SELECT: U16.5, U17.4
/USB-C data and power/USB_CONN_N: J2.A7, J2.B7, R24.1, U14.2
/USB-C data and power/USB_CONN_P: J2.A6, J2.B6, R25.1, U14.1
/USB-C data and power/USB_IN_EN: Q2.3, R32.2, U16.3
/USB-C data and power/VBUS: C32.1, C33.1, J2.A4, J2.A9, J2.B4, J2.B9, R26.1, R32.1, R34.1, U16.1, U17.3, U17.5
/USB-C data and power/VBUS_GATE: Q4.1, R34.2, R35.1
BOOT_IO8: R4.2, U1.22
BOOT_IO9: J1.5, R5.2, SW2.1, U1.23
CC_nINT: R27.2, U1.12, U13.6
CHG_ALLOW: Q1.1, R39.1, U1.26
CHG_nINT: R37.2, U1.27, U11.9
GND: C1.2, C2.2, C3.2, C5.2, C6.2, C7.2, C8.2, C9.2, C10.2, C11.2, C12.2, C13.2, C14.2, C15.2, C16.2, C17.2, C18.2, C19.2, C20.2, C21.2, C22.2, C23.2, C24.2, C25.2, C26.2, C27.2, C28.2, C29.2, C30.2, C31.2, C32.2, C33.2, C34.2, C35.2, C36.2, C37.2, C38.2, C39.2, C40.2, C41.2, C42.2, C43.2, C100.2, C101.2, C102.2, C103.2, C110.2, C111.2, C112.2, C113.2, C120.2, C121.2, C122.2, C123.2, C130.2, C131.2, C132.2, C133.2, C140.2, C141.2, C142.2, C143.2, C150.2, C151.2, C152.2, C153.2, C160.2, C161.2, C162.2, C163.2, C170.2, C171.2, C172.2, C173.2, J1.2, J2.A1, J2.A12, J2.B1, J2.B12, J2.SH, J3.2, J3.4, J100.2, J101.2, J102.2, J103.2, J104.2, J105.2, J106.2, J107.2, J108.2, J109.2, J110.2, J111.2, J112.2, J113.2, J114.2, J115.2, J116.2, J117.2, J118.2, J119.2, J120.2, J121.2, J122.2, J123.2, J124.2, J125.2, J126.2, J127.2, J128.2, J129.2, J130.2, J131.2, J200.2, J201.2, J202.2, J203.2, J204.2, J205.2, J206.2, J207.2, Q1.2, Q2.2, Q3.2, Q4.2, Q5.2, R7.2, R28.2, R30.2, R31.2, R33.2, R35.2, R39.2, R41.2, R43.2, R45.2, SW1.2, SW2.2, SW3.2, U1.1, U1.2, U1.11, U1.14, U1.36, U1.37, U1.38, U1.39, U1.40, U1.41, U1.42, U1.43, U1.44, U1.45, U1.46, U1.47, U1.48, U1.49, U1.50, U1.51, U1.52, U1.53, U3.B3, U4.B3, U5.B3, U6.B3, U7.B3, U8.B3, U9.B3, U10.B3, U11.5, U11.11, U12.2, U12.3, U12.8, U13.3, U13.5, U13.10, U13.11, U14.3, U15.3, U16.2, U17.2, U18.7, U19.7, U20.7, U21.7, U22.7, U23.7, U24.7, U25.7, U26.2
I2C_SCL: R2.2, U1.16, U11.8, U13.8
I2C_SDA: R1.2, U1.15, U11.7, U13.7
LED_B_N: R51.1, R52.2, U1.20
LED_G_N: R49.1, R50.2, U1.10
LED_R_N: R47.1, R48.2, U1.9
MCU_EN: C1.1, J1.6, R3.2, SW1.1, U1.8
POD_3V3: C5.1, C7.1, C8.1, C10.1, C11.1, C13.1, C14.1, C16.1, C17.1, C19.1, C20.1, C22.1, C23.1, C25.1, C26.1, C28.1, C43.1, C100.1, C101.1, C103.1, C110.1, C111.1, C113.1, C120.1, C121.1, C123.1, C130.1, C131.1, C133.1, C140.1, C141.1, C143.1, C150.1, C151.1, C153.1, C160.1, C161.1, C163.1, C170.1, C171.1, C173.1, J100.1, J101.1, J102.1, J104.1, J105.1, J106.1, J108.1, J109.1, J110.1, J112.1, J113.1, J114.1, J116.1, J117.1, J118.1, J120.1, J121.1, J122.1, J124.1, J125.1, J126.1, J128.1, J129.1, J130.1, R6.1, R8.1, R9.1, R10.1, R11.1, R12.1, R13.1, R14.1, R15.1, R16.1, R17.1, R18.1, R19.1, R20.1, R21.1, R22.1, R23.1, R46.1, R102.1, R103.1, R105.1, R112.1, R113.1, R115.1, R122.1, R123.1, R125.1, R132.1, R133.1, R135.1, R142.1, R143.1, R145.1, R152.1, R153.1, R155.1, R162.1, R163.1, R165.1, R172.1, R173.1, R175.1, U3.B2, U3.C2, U4.B2, U4.C2, U5.B2, U5.C2, U6.B2, U6.C2, U7.B2, U7.C2, U8.B2, U8.C2, U9.B2, U9.C2, U10.B2, U10.C2, U18.9, U19.9, U20.9, U21.9, U22.9, U23.9, U24.9, U25.9, U26.6
POD_POWER_ON: R45.1, U1.6, U26.3
RING_D0: J100.3, R42.2, R100.1
RING_D1: J101.3, J104.3, R101.2, R110.1
RING_D2: J105.3, J108.3, R111.2, R120.1
RING_D3: J109.3, J112.3, R121.2, R130.1
RING_D4: J113.3, J116.3, R131.2, R140.1
RING_D5: J117.3, J120.3, R141.2, R150.1
RING_D6: J121.3, J124.3, R151.2, R160.1
RING_D7: J125.3, J128.3, R161.2, R170.1
RING_D8: J129.3, R53.1, R171.2
RING_RESET_ASSERT: Q5.1, R7.1, U1.24
RING_RETURN: J100.6, J101.6, J104.6, J105.6, J108.6, J109.6, J112.6, J113.6, J116.6, J117.6, J120.6, J121.6, J124.6, J125.6, J128.6, J129.6, R53.2, U1.5
RING_nRESET: C40.1, J100.4, J101.4, J102.5, J104.4, J105.4, J106.5, J108.4, J109.4, J110.5, J112.4, J113.4, J114.5, J116.4, J117.4, J118.5, J120.4, J121.4, J122.5, J124.4, J125.4, J126.5, J128.4, J129.4, J130.5, R6.2, R44.1, U18.4, U19.4, U20.4, U21.4, U22.4, U23.4, U24.4, U25.4
UART_RX: J1.4, U1.30
UART_TX: J1.3, U1.31
USB_5V_LIMITED: C34.1, U11.10, U16.6
USB_D_N: C29.1, R24.2, U1.17
USB_D_P: C30.1, R25.2, U1.18
USB_INPUT_OFF: Q2.1, R33.1, U1.19
USB_LIMIT_ENABLE: R31.1, U1.28, U17.6
USB_LIMIT_HIGH: Q3.1, R30.1, U1.29
VBAT: C36.1, F100.2, F101.2, F102.2, F103.2, F104.2, F105.2, F106.2, F107.2, J3.1, J100.5, J101.5, J104.5, J105.5, J108.5, J109.5, J112.5, J113.5, J116.5, J117.5, J120.5, J121.5, J124.5, J125.5, J128.5, J129.5, U11.2
VBUS_nPRESENT: Q4.3, R36.2, U1.13
